drolsen/r2-periscope-lighting/assets/329545608_787965672744725_6274756382446998842_n.jpg

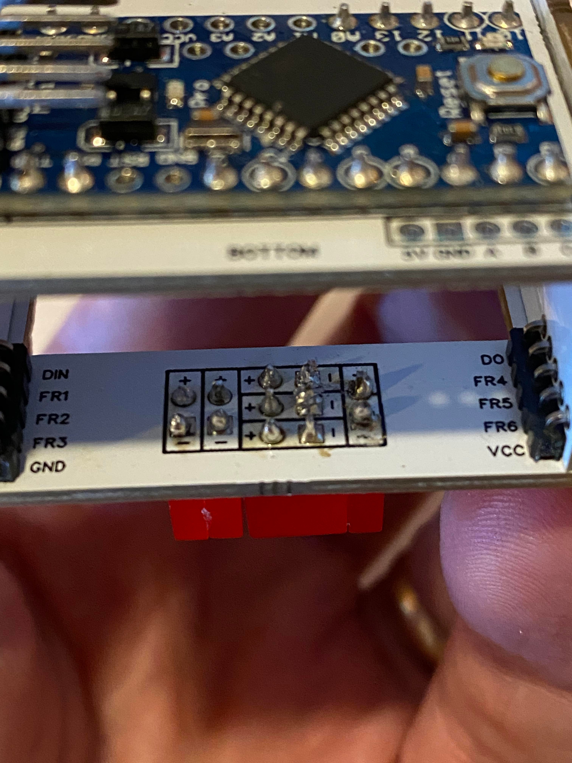
assets/329545608_787965672744725_6274756382446998842_n.jpg
