drolsen/r2-periscope-lighting/assets/329946529_3398057897189218_7023022062316048752_n.jpg

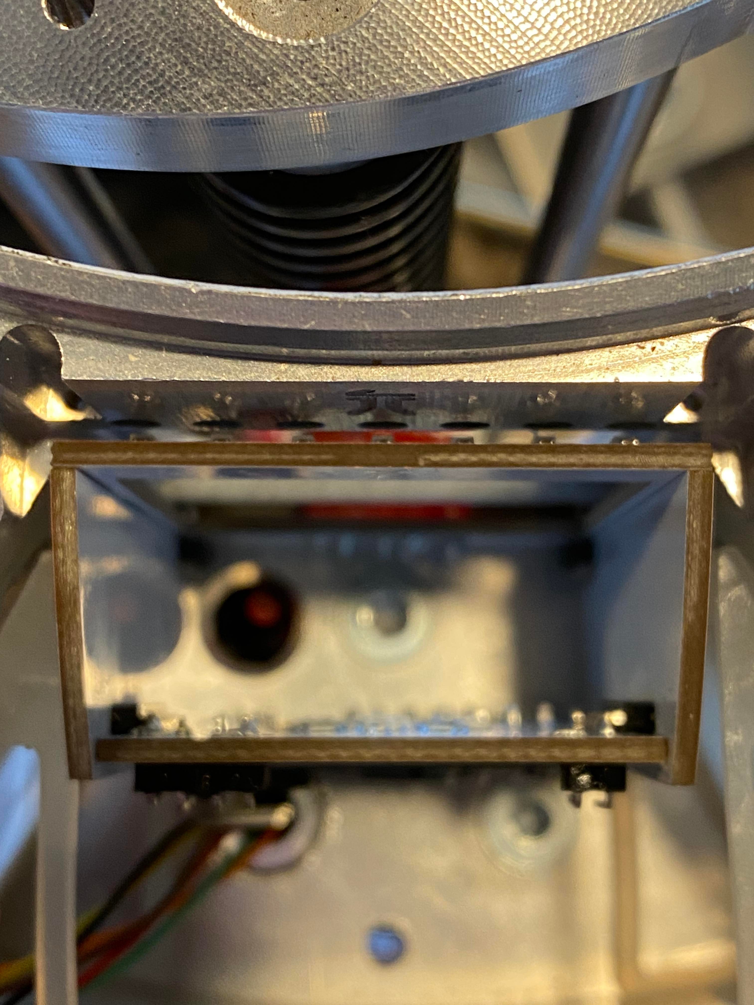
assets/329946529_3398057897189218_7023022062316048752_n.jpg
