drolsen/r2-periscope-lighting/assets/330140581_1176772722986566_4878100854022843440_n.jpg

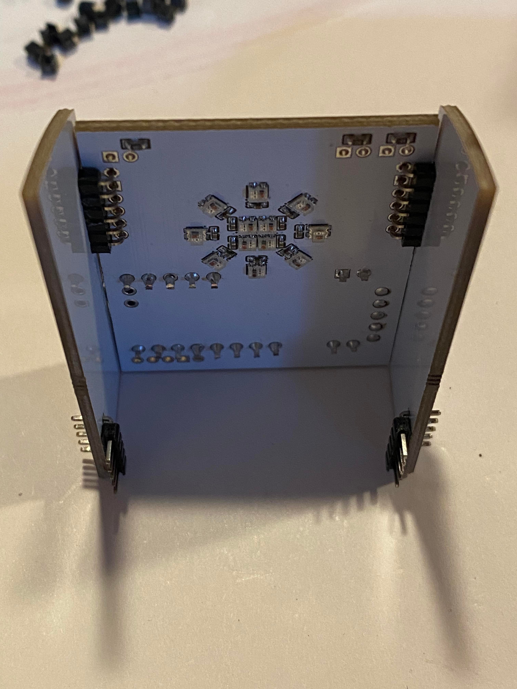
assets/330140581_1176772722986566_4878100854022843440_n.jpg
