drolsen/r2-periscope-lighting/assets/330237637_755844602558149_2887679224350733266_n.jpg

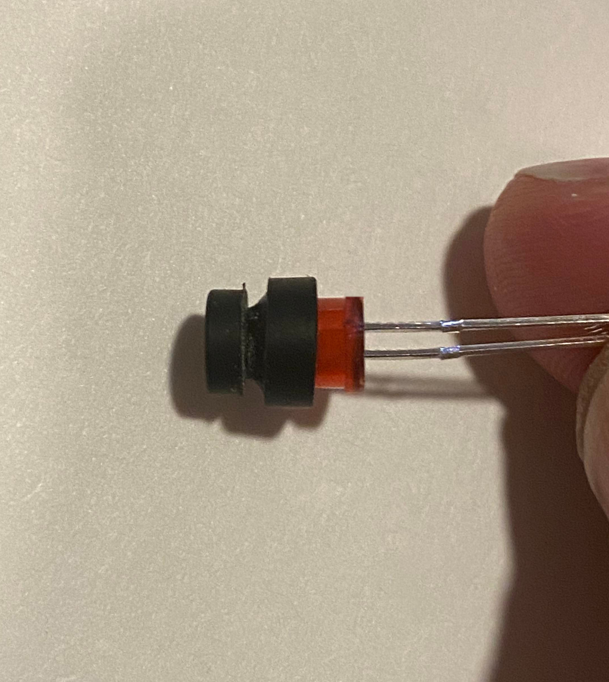
assets/330237637_755844602558149_2887679224350733266_n.jpg
