drolsen/r2-periscope-lighting/assets/336583348_1359087688268393_5020265776512630754_n.jpg

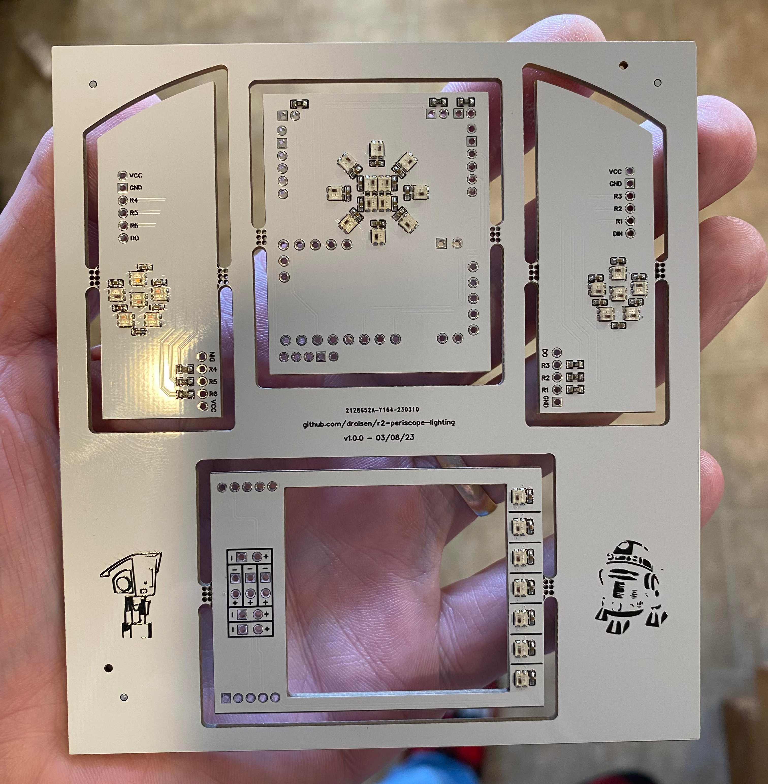
assets/336583348_1359087688268393_5020265776512630754_n.jpg
