drolsen/r2-periscope-lighting/assets/336612819_212626751346607_8498144002809746139_n.jpg

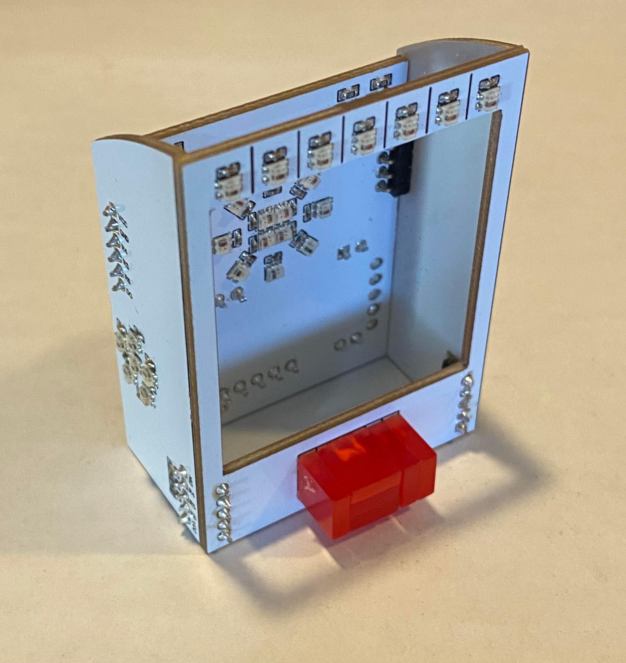
assets/336612819_212626751346607_8498144002809746139_n.jpg
