drolsen/r2-periscope-lighting/assets/336630692_2085747125148480_5399964535549881073_n.jpg

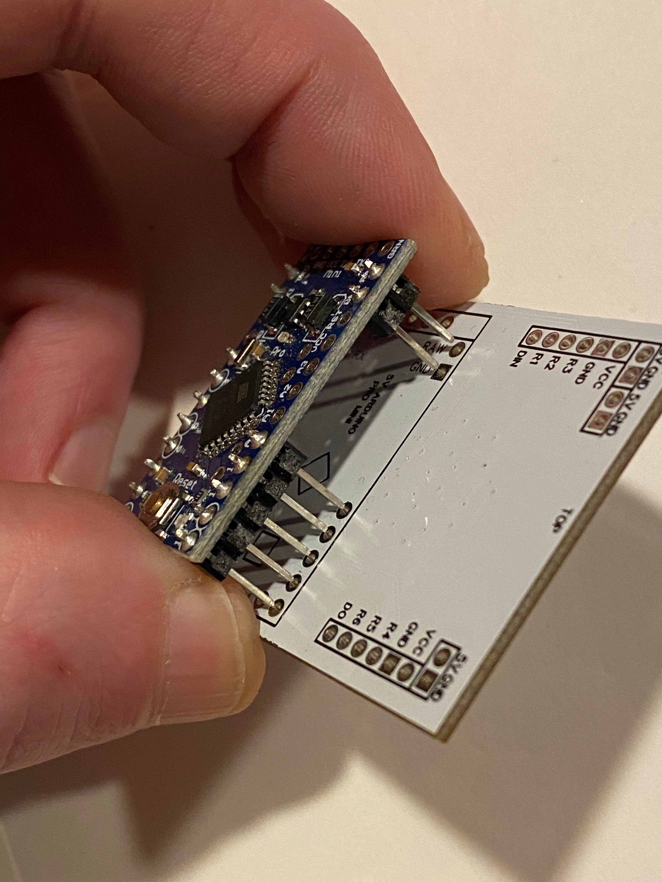
assets/336630692_2085747125148480_5399964535549881073_n.jpg
