drolsen/r2-periscope-lighting/assets/336634593_1632840413847791_8833610450574456791_n.jpg

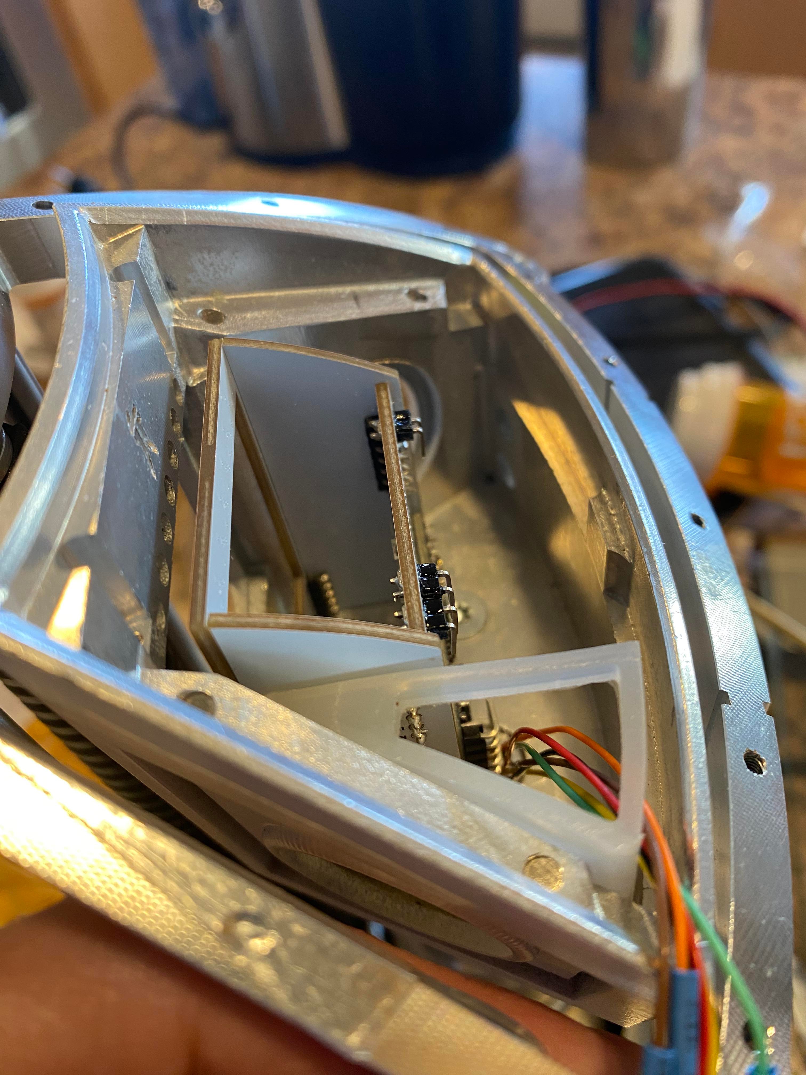
assets/336634593_1632840413847791_8833610450574456791_n.jpg
