drolsen/r2-periscope-lighting/assets/336643133_749938070041461_5090229318301993408_n.jpg

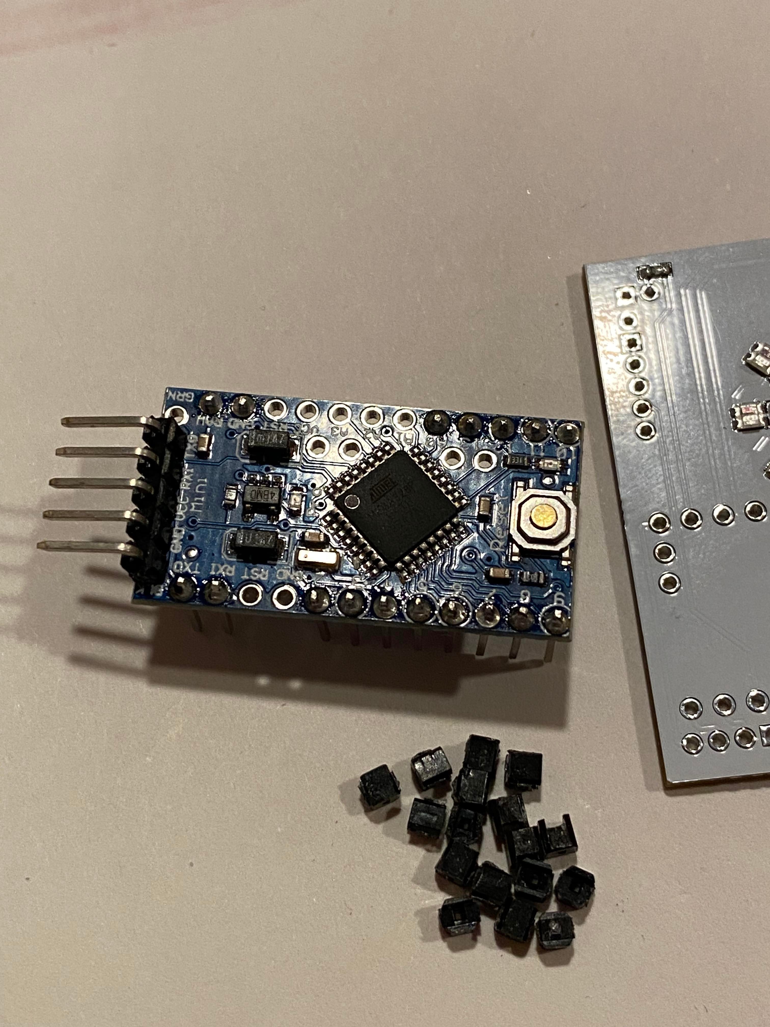
assets/336643133_749938070041461_5090229318301993408_n.jpg
