drolsen/r2-periscope-lighting/assets/336646238_229451316157610_1500926734936999446_n.jpg

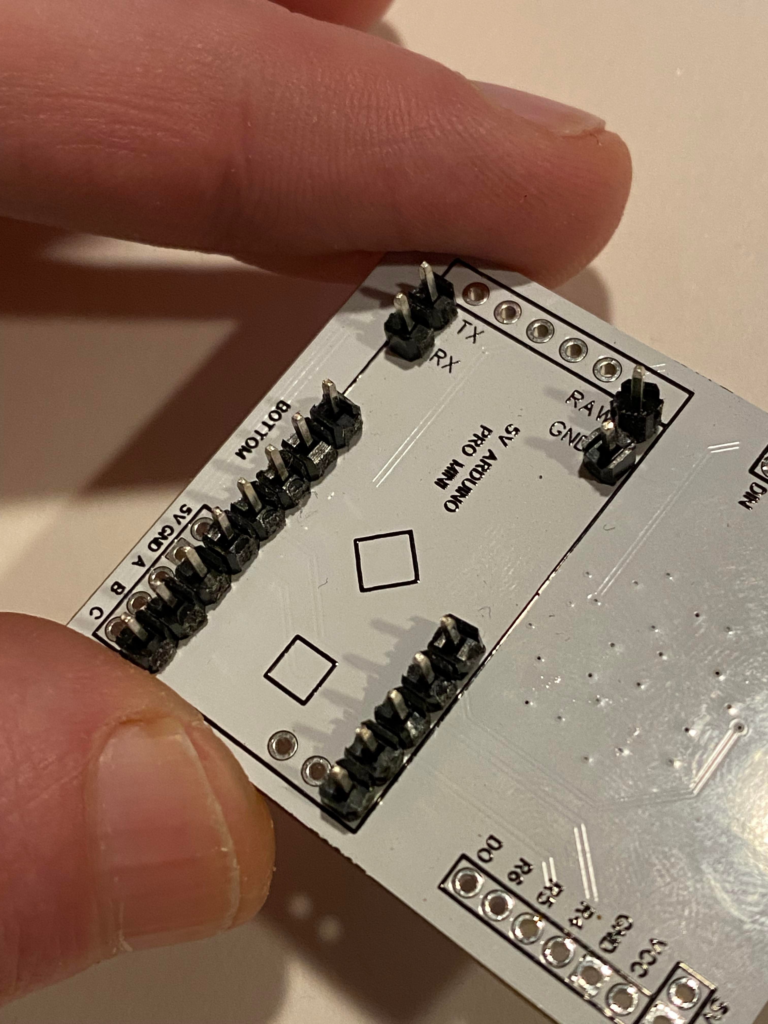
assets/336646238_229451316157610_1500926734936999446_n.jpg
