drolsen/r2-periscope-lighting/assets/336648805_155341664117025_93847598374509q8374_n.jpg

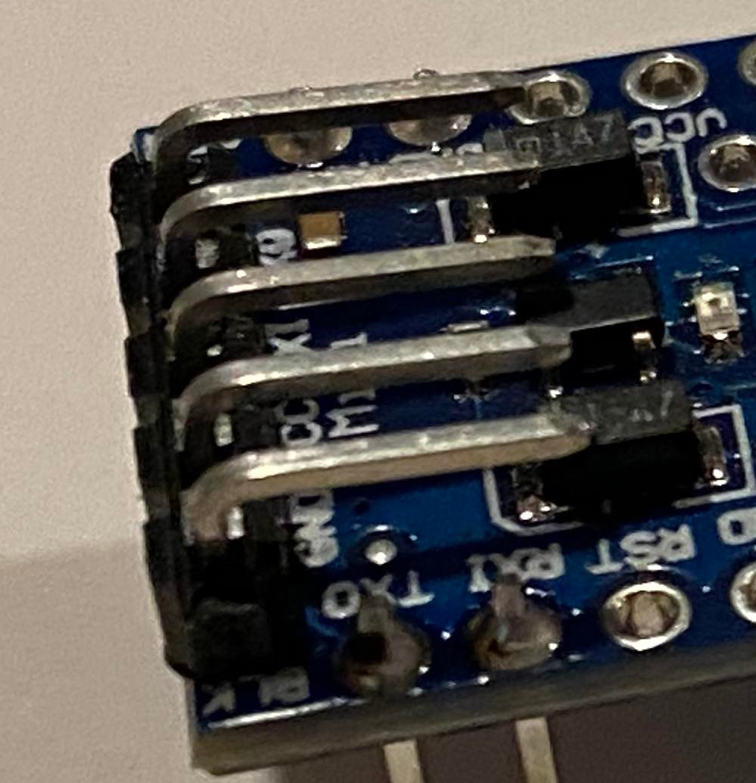
assets/336648805_155341664117025_93847598374509q8374_n.jpg
