drolsen/r2-periscope-lighting/assets/336648805_155341664117025_7592663786943222012_n.jpg

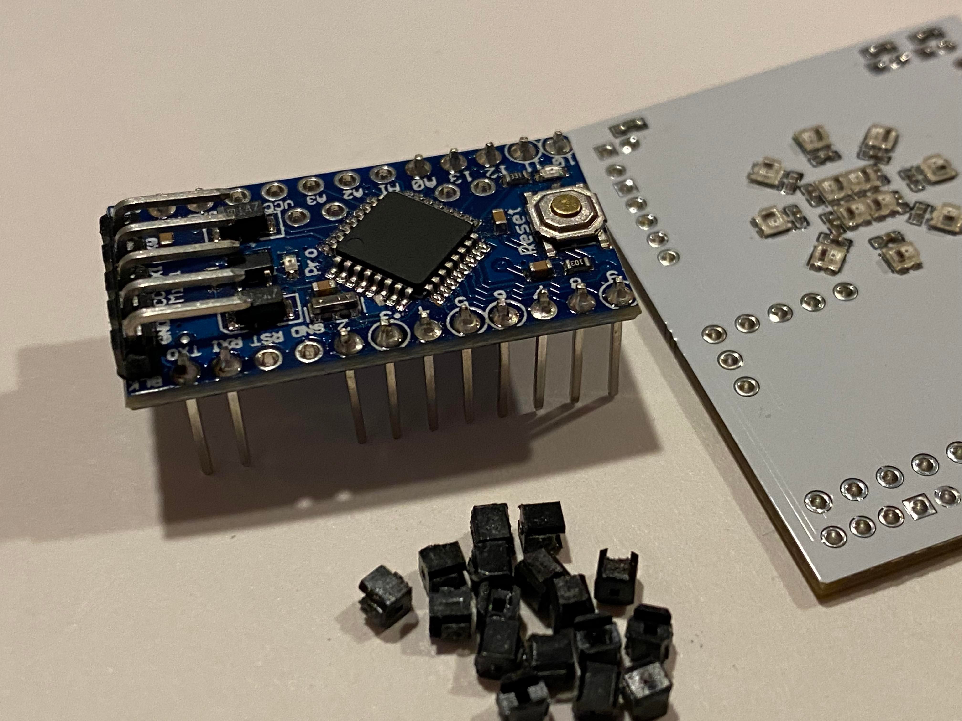
assets/336648805_155341664117025_7592663786943222012_n.jpg
