drolsen/r2-periscope-lighting/assets/336650088_955661678923347_95887453174213963_n.jpg

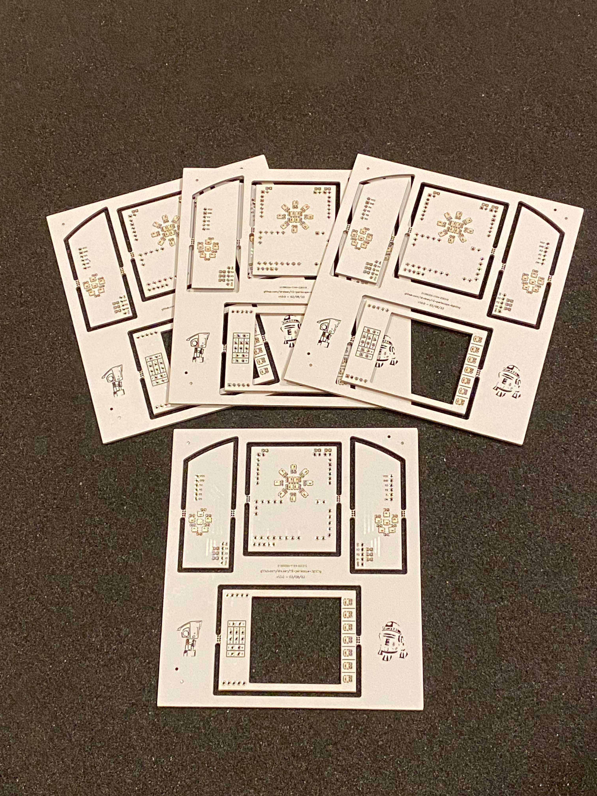
assets/336650088_955661678923347_95887453174213963_n.jpg
