drolsen/r2-periscope-lighting/assets/336652210_146992861645513_2133253247922061453_n.jpg

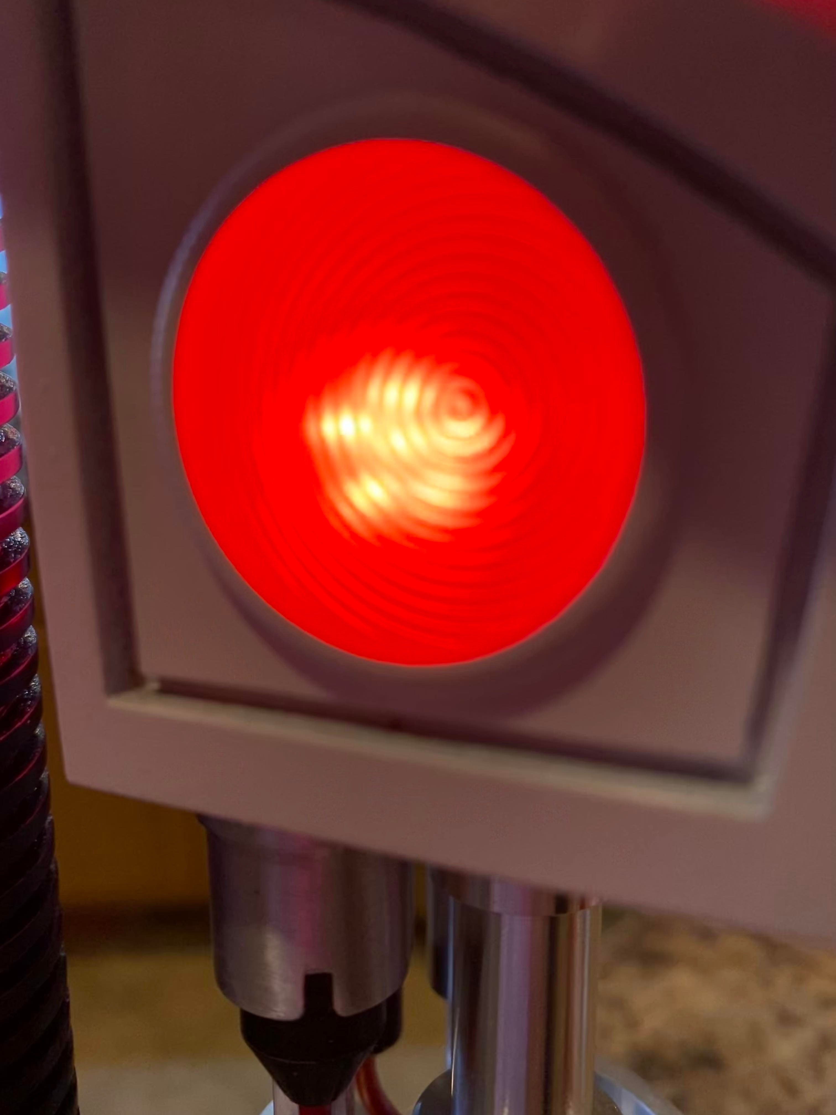
assets/336652210_146992861645513_2133253247922061453_n.jpg
