drolsen/r2-periscope-lighting/assets/336652988_1221817398455848_6877816285766562561_n.jpg

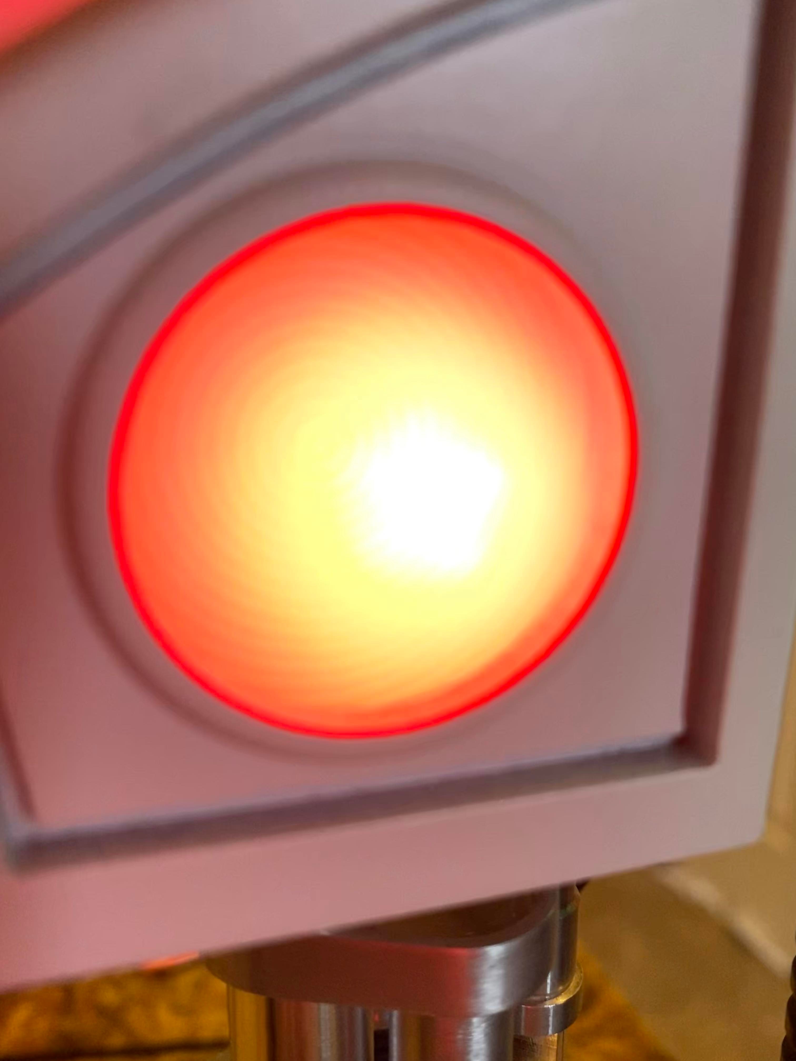
assets/336652988_1221817398455848_6877816285766562561_n.jpg
