drolsen/r2-periscope-lighting/assets/336654507_557893633128408_7048110893152010657_n.jpg

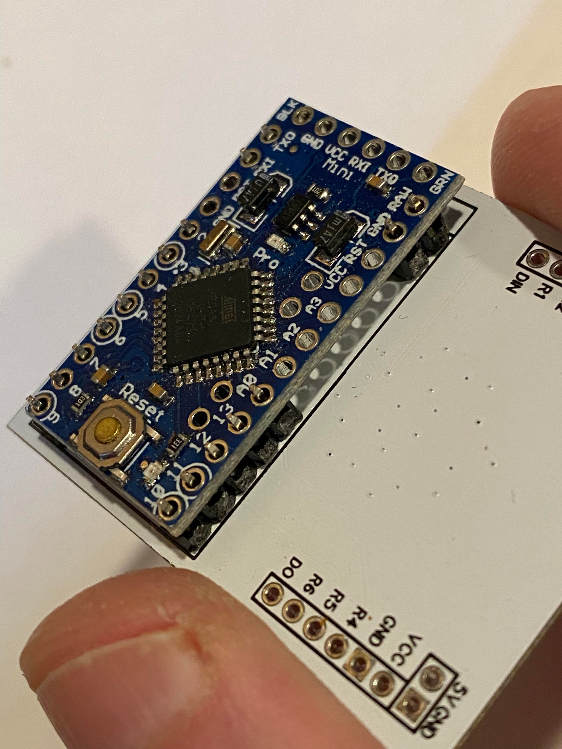
assets/336654507_557893633128408_7048110893152010657_n.jpg
