drolsen/r2-periscope-lighting/assets/336655963_2727371454069084_6634626331095543156_n.jpg

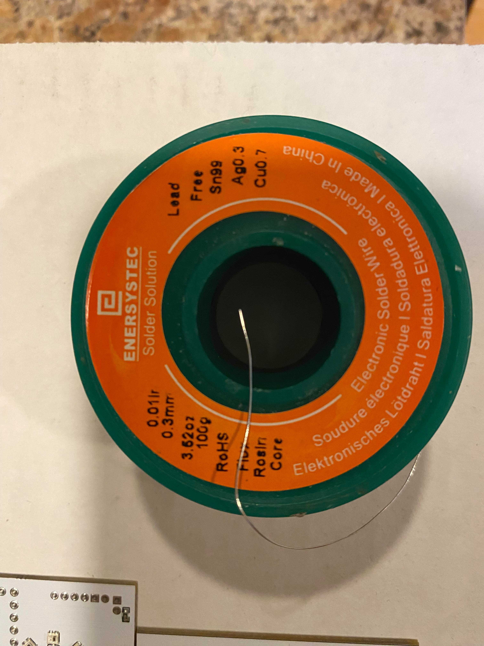
assets/336655963_2727371454069084_6634626331095543156_n.jpg
