drolsen/r2-periscope-lighting/assets/336656577_208245721811248_5027375010276381382_n.jpg

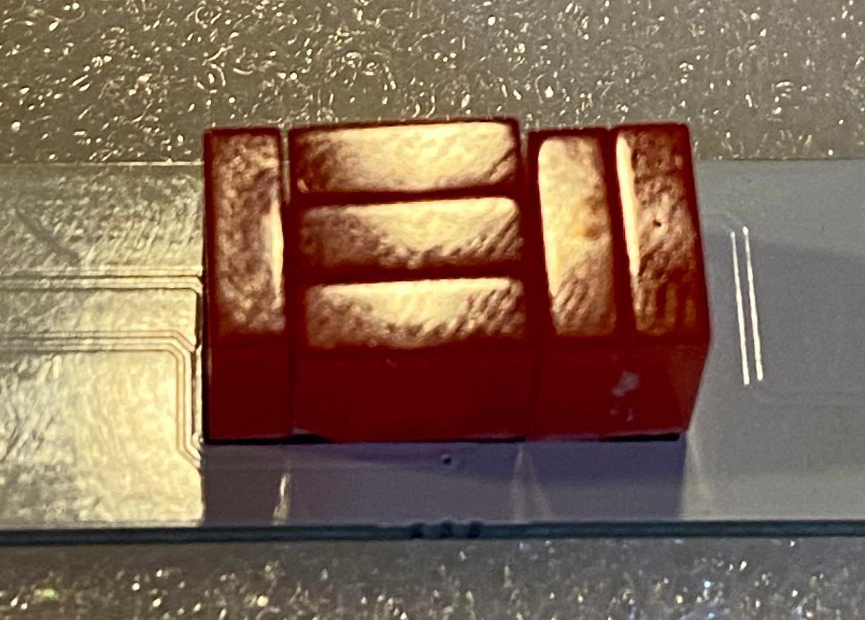
assets/336656577_208245721811248_5027375010276381382_n.jpg
