drolsen/r2-periscope-lighting/assets/336674563_130055486537326_960620624127797083_n.jpg

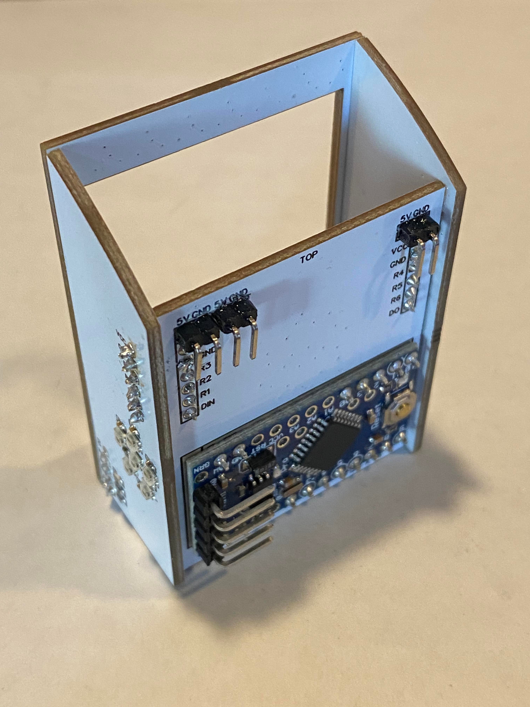
assets/336674563_130055486537326_960620624127797083_n.jpg
