drolsen/r2-periscope-lighting/assets/336676215_763743515095781_526933514709805942_n.jpg

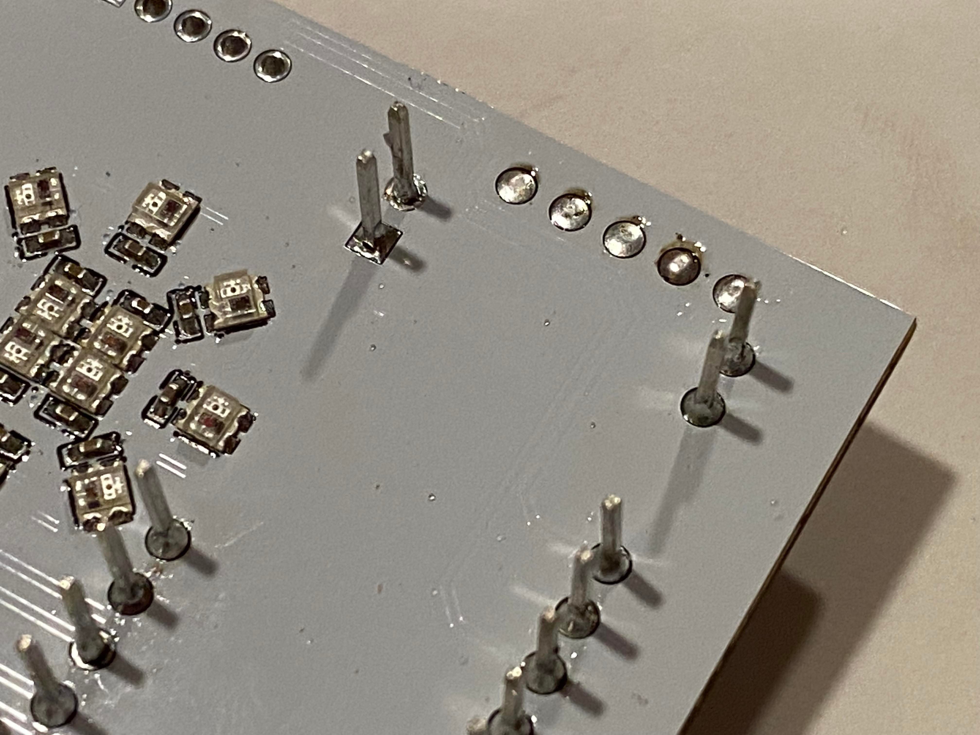
assets/336676215_763743515095781_526933514709805942_n.jpg
