drolsen/r2-periscope-lighting/assets/336676218_1423926755043374_4888183736791401821_n.jpg

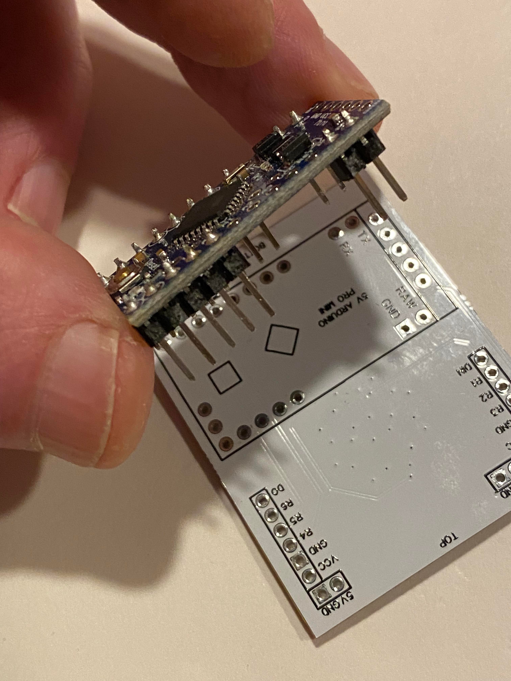
assets/336676218_1423926755043374_4888183736791401821_n.jpg
