drolsen/r2-periscope-lighting/assets/336762101_140780122016754_2259027312010947617_n.jpg

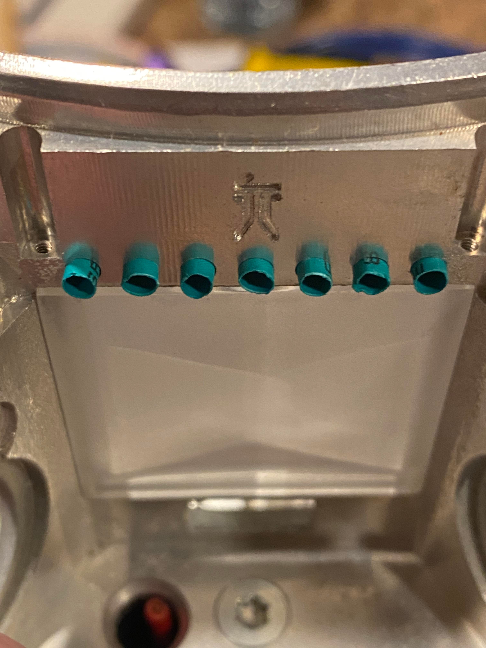
assets/336762101_140780122016754_2259027312010947617_n.jpg
