drolsen/r2-periscope-lighting/assets/336774285_554087970160996_1432412874619068593_n.jpg

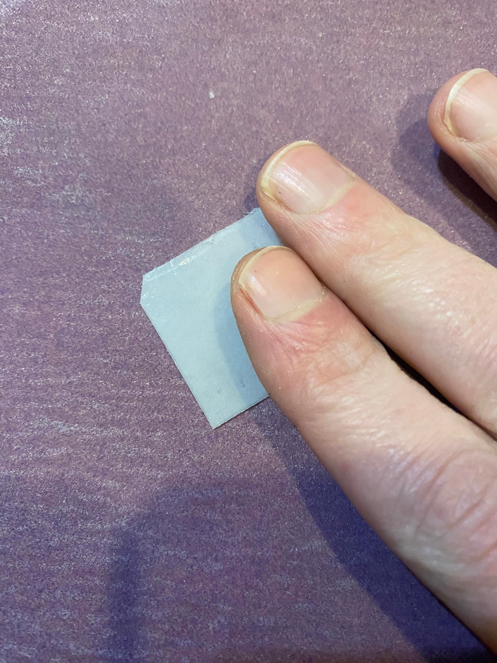
assets/336774285_554087970160996_1432412874619068593_n.jpg
