drolsen/r2-periscope-lighting/assets/336782065_769995744817289_480746282116714506_n.jpg

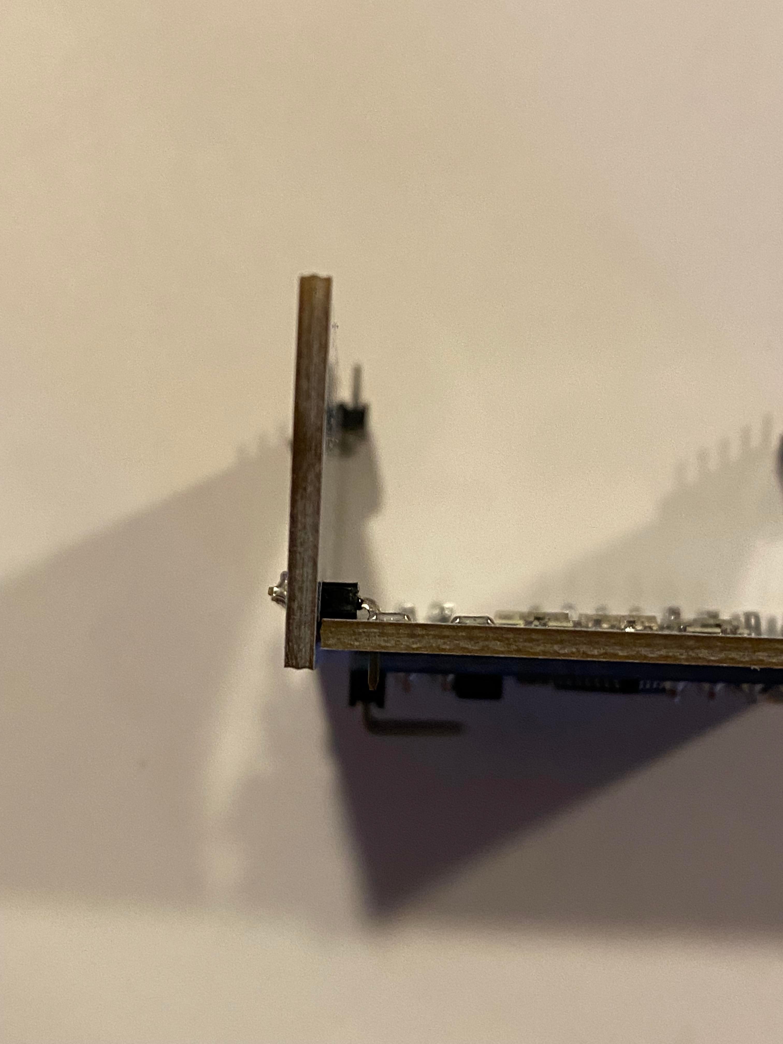
assets/336782065_769995744817289_480746282116714506_n.jpg
