drolsen/r2-periscope-lighting/assets/336802224_611826760356297_9049021178184410833_n.jpg

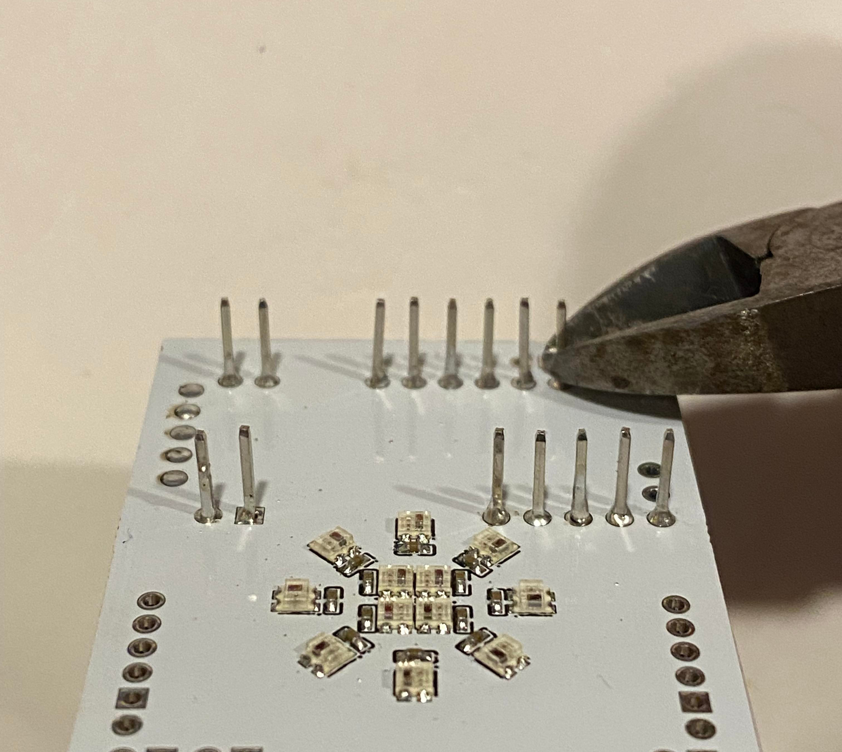
assets/336802224_611826760356297_9049021178184410833_n.jpg
