drolsen/r2-periscope-lighting/assets/336858418_887466352534189_1731890954181260684_n.jpg

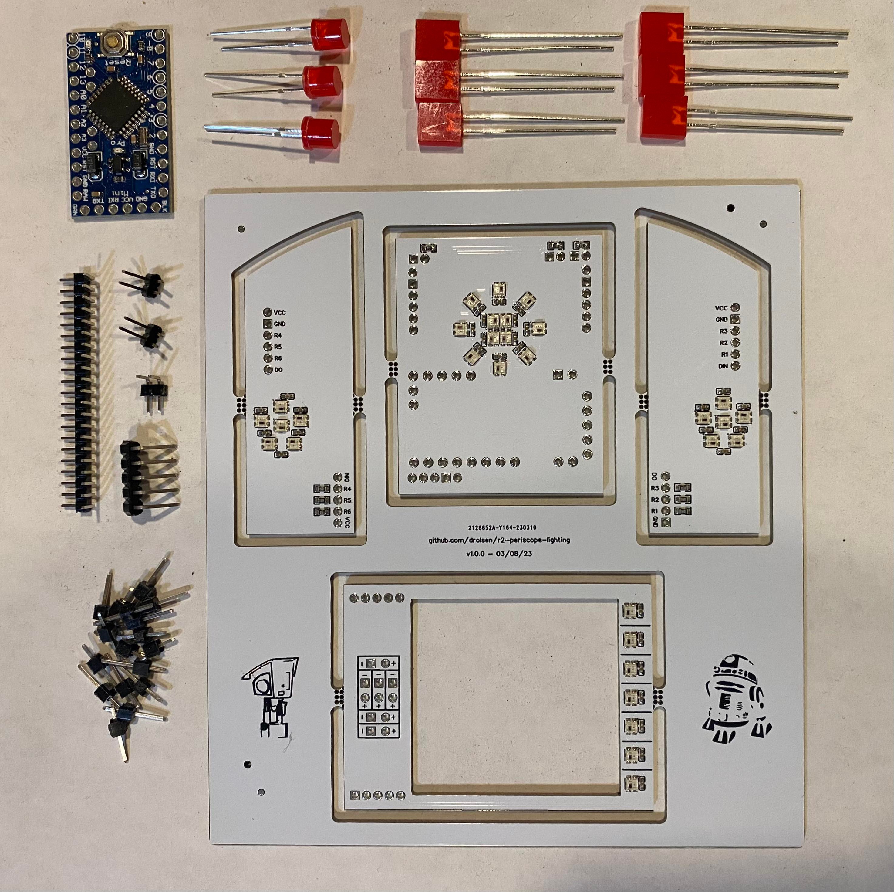
assets/336858418_887466352534189_1731890954181260684_n.jpg
