drolsen/r2-periscope-lighting/assets/336882048_944176487019811_1727440528449711896_n.jpg

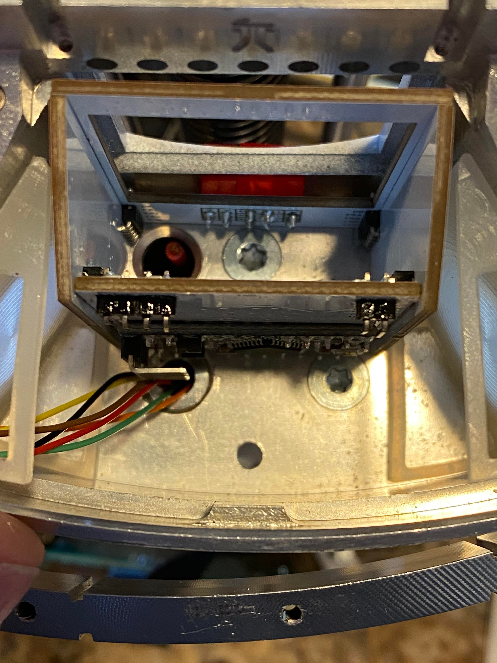
assets/336882048_944176487019811_1727440528449711896_n.jpg
