drolsen/r2-periscope-lighting/assets/336910001_962262608291722_509679109615035891_n.jpg

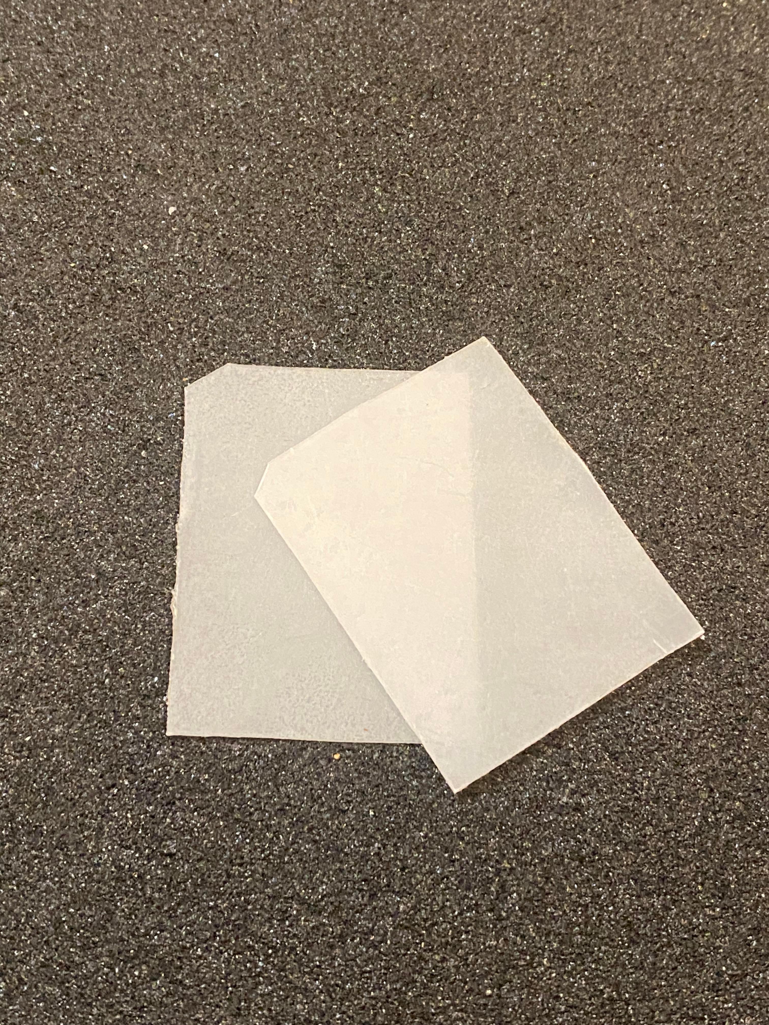
assets/336910001_962262608291722_509679109615035891_n.jpg
