drolsen/r2-periscope-lighting/assets/336953458_753239979686228_8079525611871128589_n.jpg

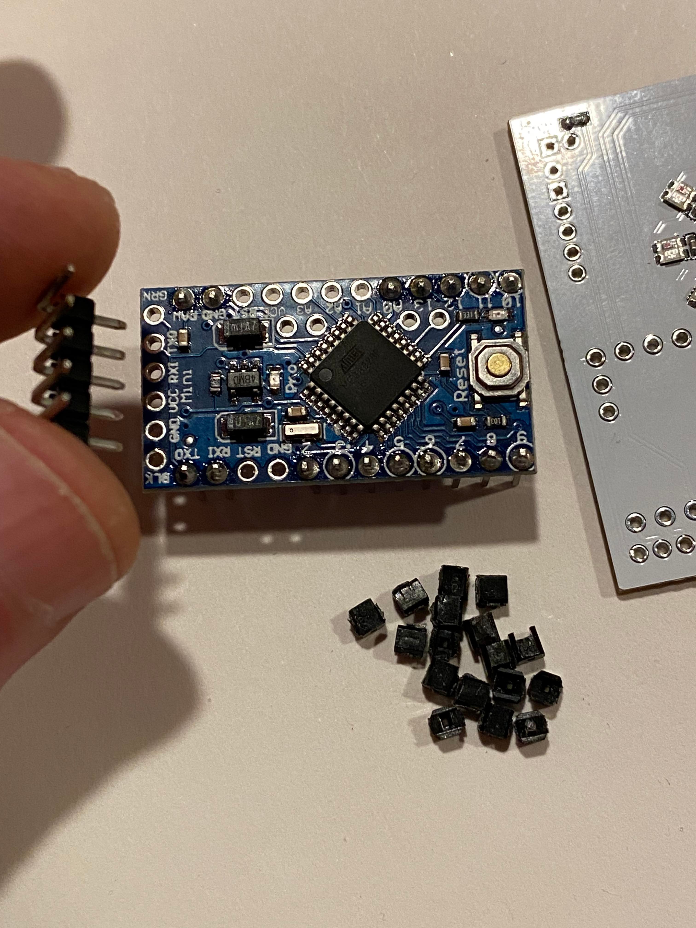
assets/336953458_753239979686228_8079525611871128589_n.jpg
