drolsen/r2-periscope-lighting/assets/336954538_926445541840880_992458918952481467_n.jpg

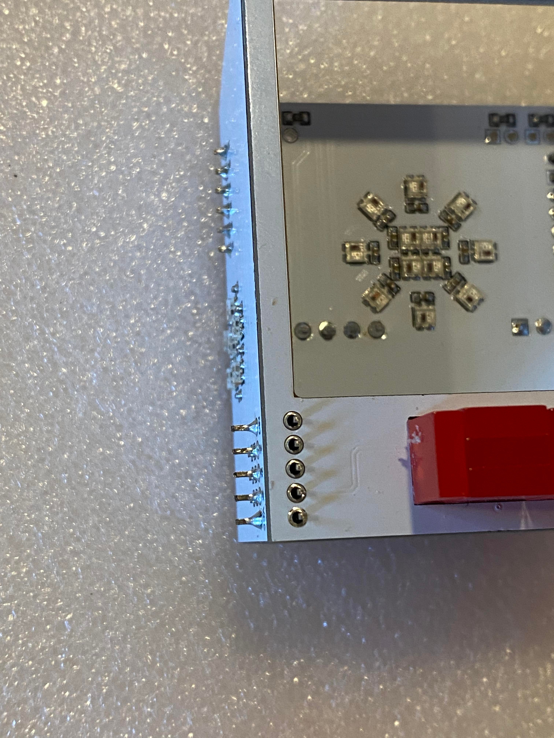
assets/336954538_926445541840880_992458918952481467_n.jpg
