drolsen/r2-periscope-lighting/assets/336974737_1384300059000098_4011215609476208007_n.jpg

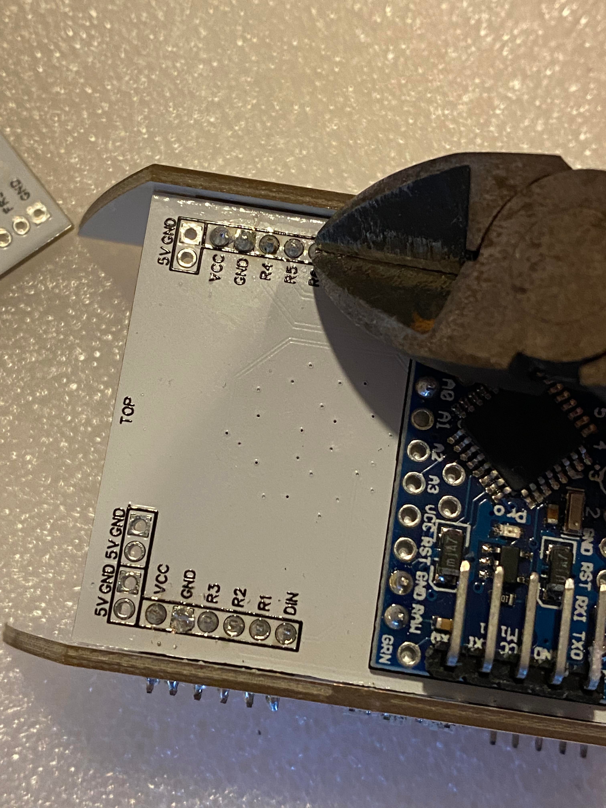
assets/336974737_1384300059000098_4011215609476208007_n.jpg
