drolsen/r2-periscope-lighting/assets/336978709_178584938370956_5981600598084434066_n.jpg

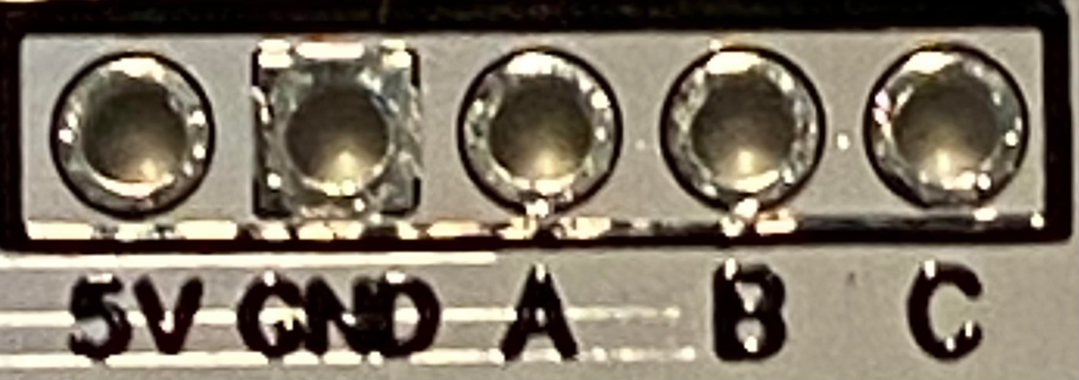
assets/336978709_178584938370956_5981600598084434066_n.jpg
