drolsen/r2-periscope-lighting/assets/336988302_238451835223995_1839003701058926174_n.jpg

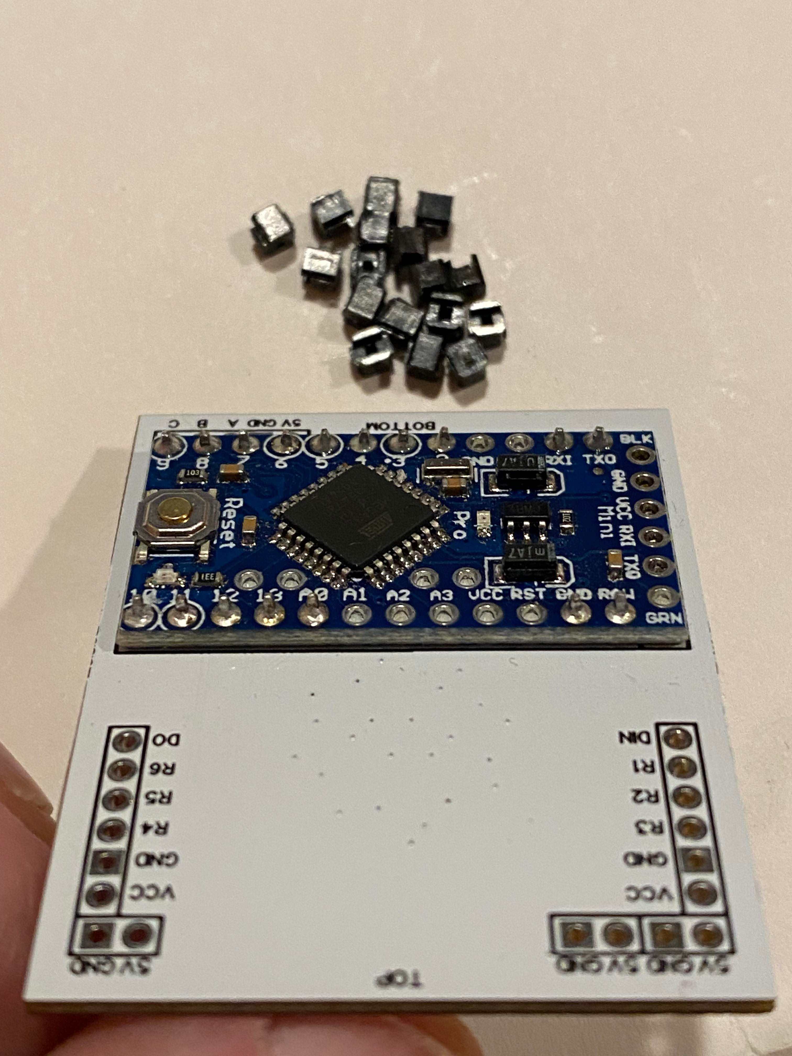
assets/336988302_238451835223995_1839003701058926174_n.jpg
