drolsen/r2-periscope-lighting/assets/337053296_767745125006024_4273821033584691869_n.jpg

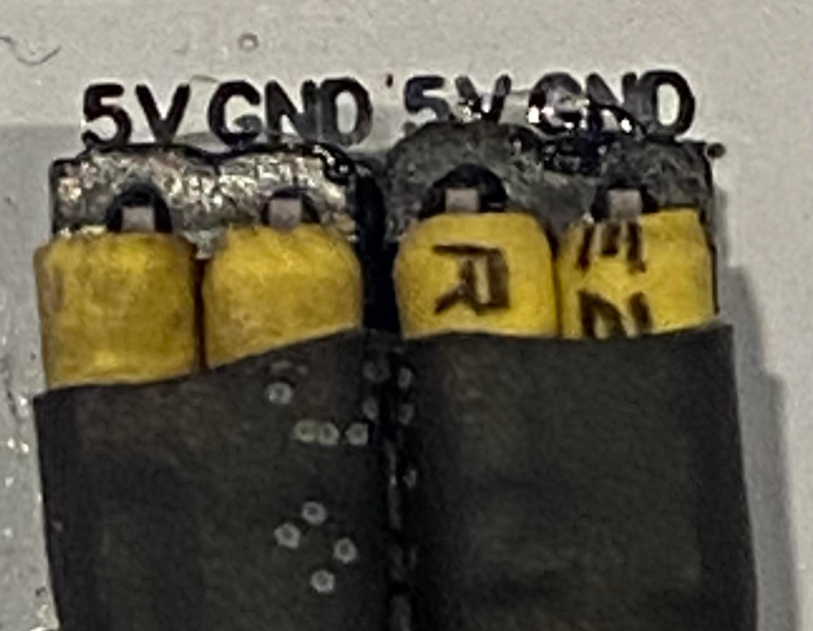
assets/337053296_767745125006024_4273821033584691869_n.jpg
