drolsen/r2-periscope-lighting/assets/337059061_1343841169793391_681237589327290217_n.jpg

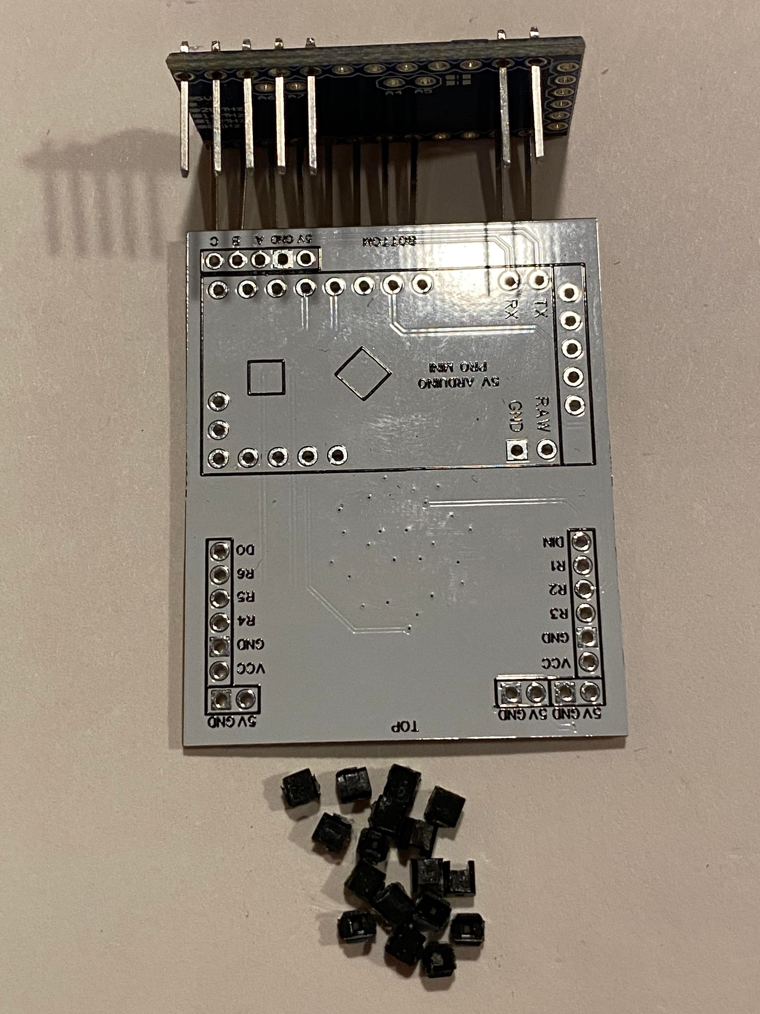
assets/337059061_1343841169793391_681237589327290217_n.jpg
