drolsen/r2-periscope-lighting/assets/337076968_3467573620138446_7653698219763336375_n.jpg

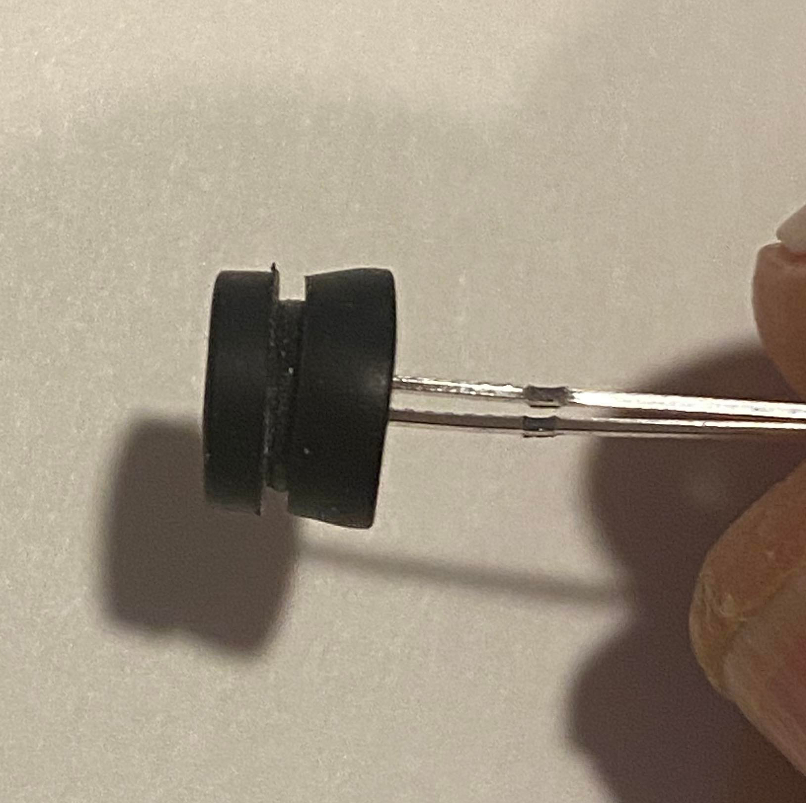
assets/337076968_3467573620138446_7653698219763336375_n.jpg
