drolsen/r2-periscope-lighting/assets/337102311_602154998597523_8643629842244105431_n.jpg

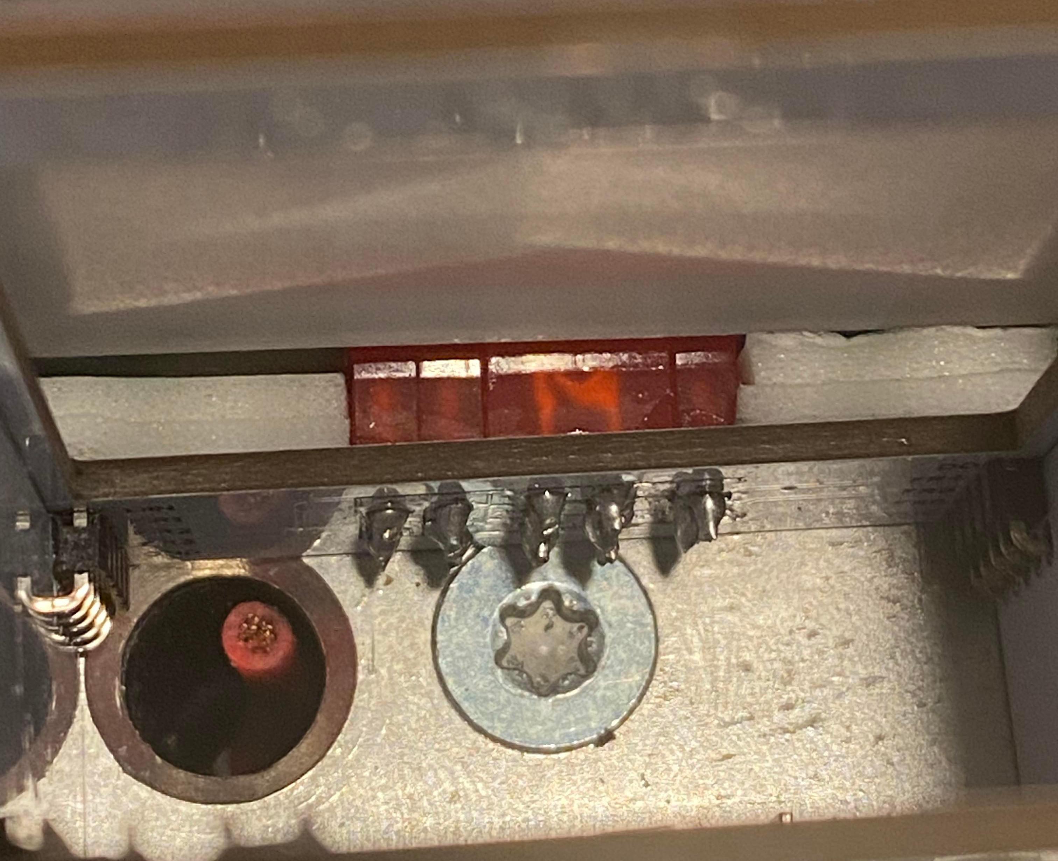
assets/337102311_602154998597523_8643629842244105431_n.jpg
