drolsen/r2-periscope-lighting/assets/337125022_598823498791530_1503493334196940726_n.jpg

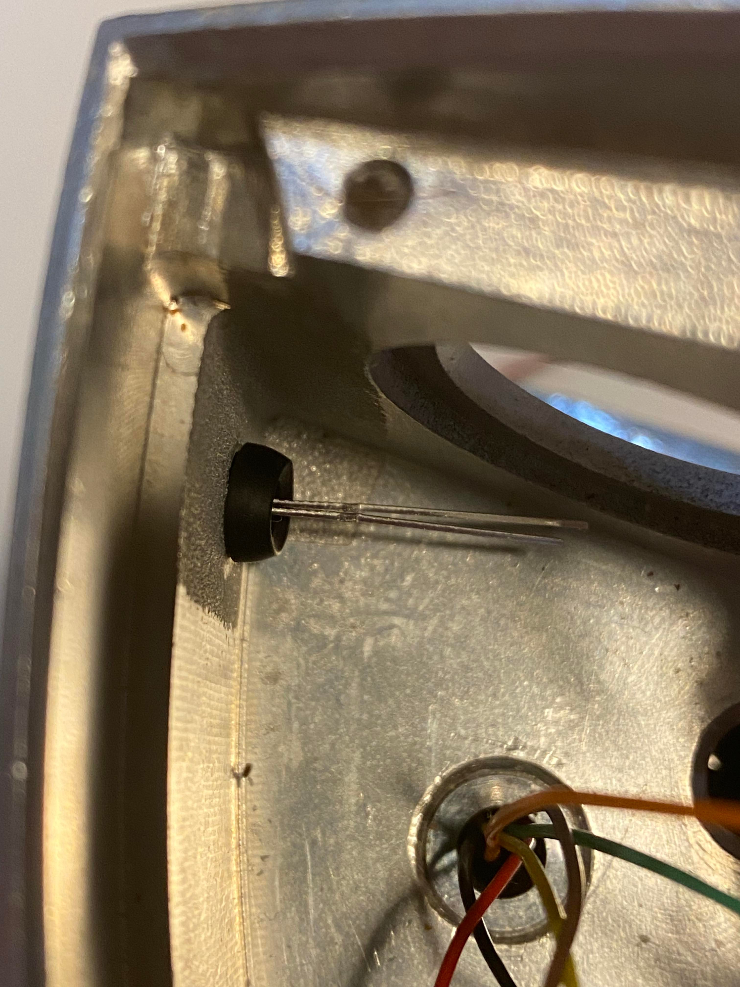
assets/337125022_598823498791530_1503493334196940726_n.jpg
