drolsen/r2-periscope-lighting/assets/337131278_3404263986559335_6530123598595243677_n.jpg

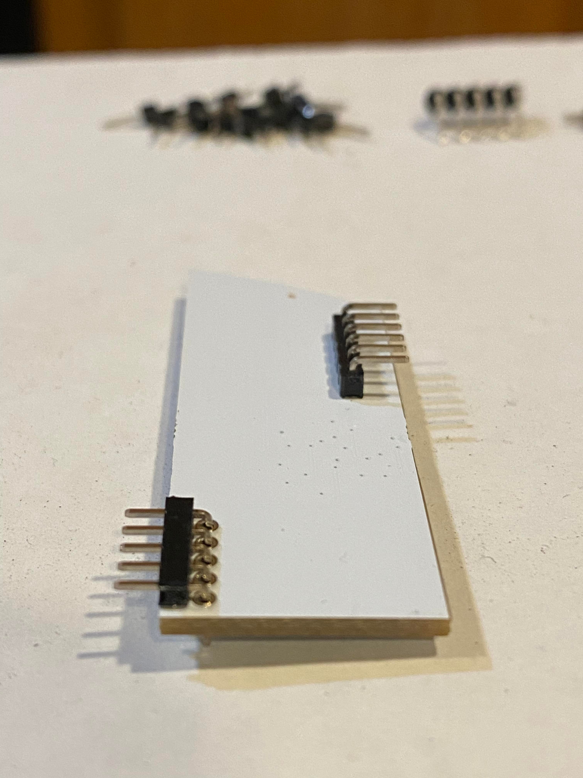
assets/337131278_3404263986559335_6530123598595243677_n.jpg
