drolsen/r2-periscope-lighting/assets/337312702_767708518035120_4002510822152139871_n.jpg

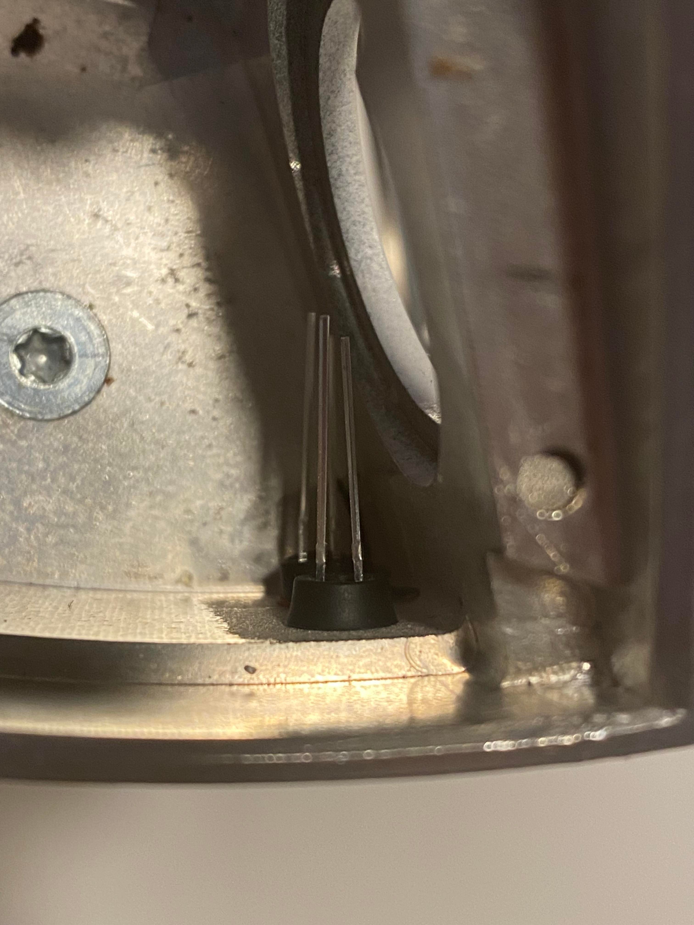
assets/337312702_767708518035120_4002510822152139871_n.jpg
