drolsen/r2-periscope-lighting/assets/337326929_697354182076062_739278119979212391_n.jpg

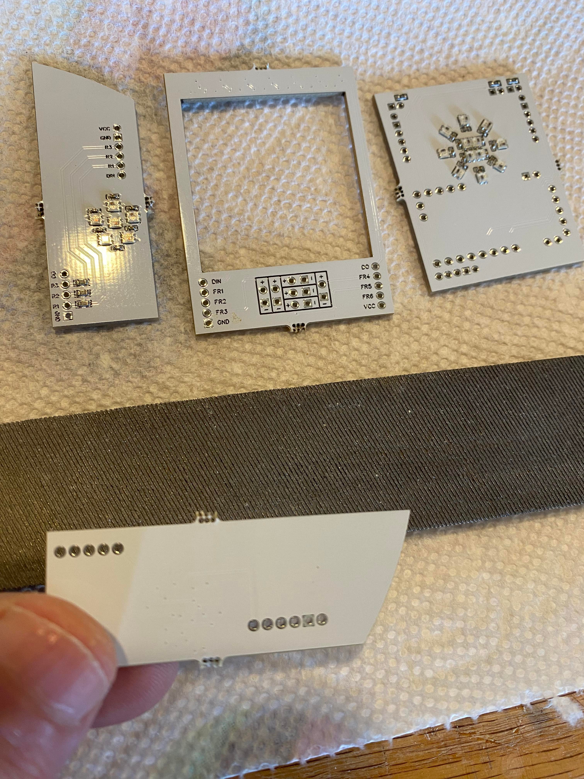
assets/337326929_697354182076062_739278119979212391_n.jpg
