drolsen/r2-periscope-lighting/assets/337430665_1330191880890299_2164580880244630802_n.jpg

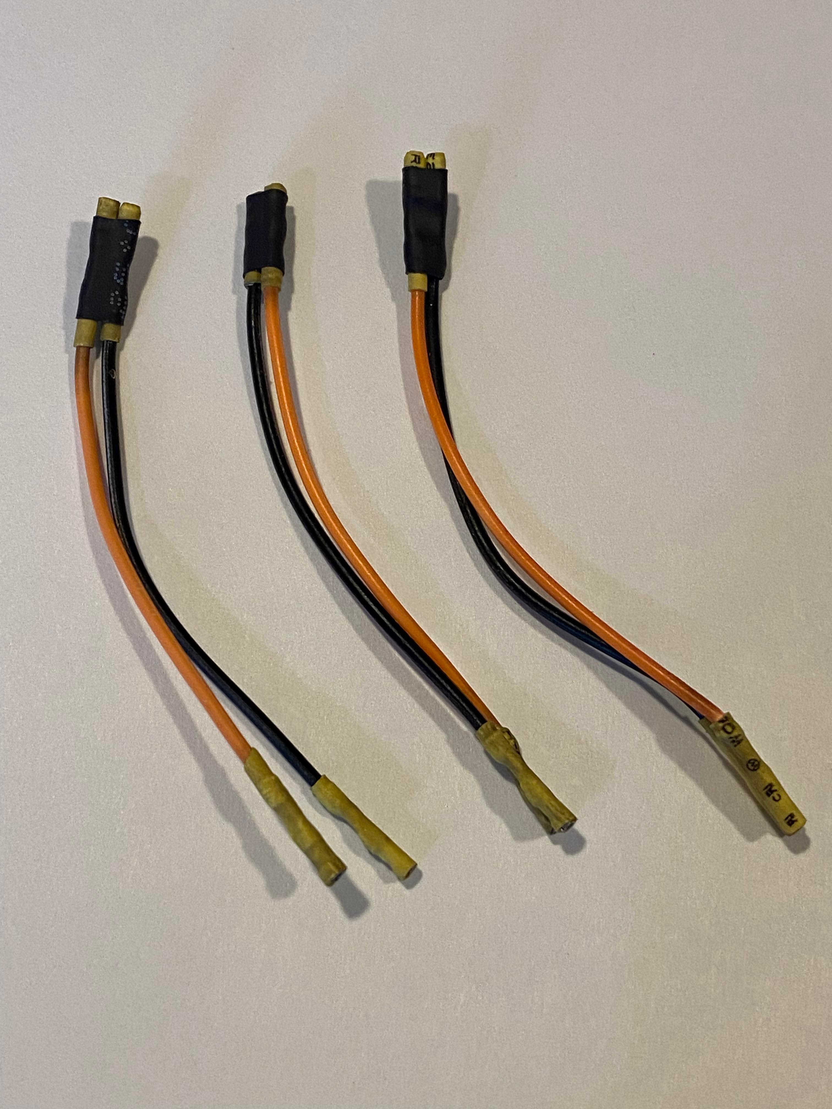
assets/337430665_1330191880890299_2164580880244630802_n.jpg
