drolsen/r2-periscope-lighting/assets/337437426_1242780033338704_8607743882371158958_n.jpg

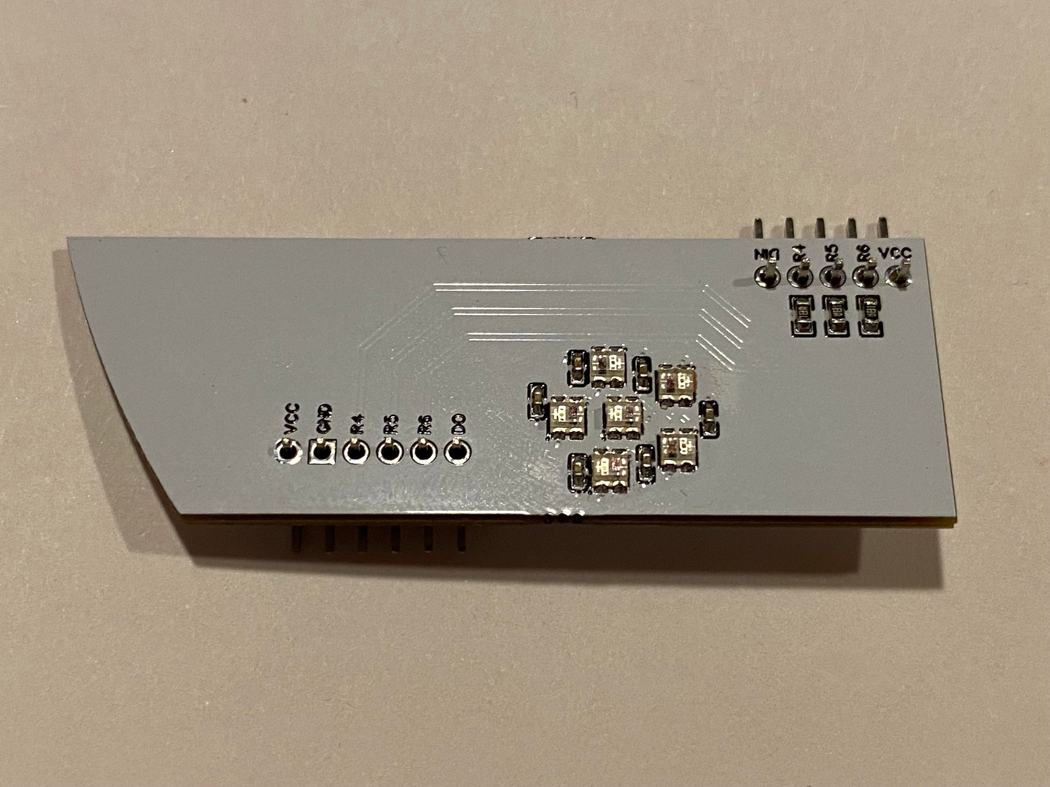
assets/337437426_1242780033338704_8607743882371158958_n.jpg
