drolsen/r2-periscope-lighting/assets/337509834_1648580835579013_2345284703102061359_n.jpg

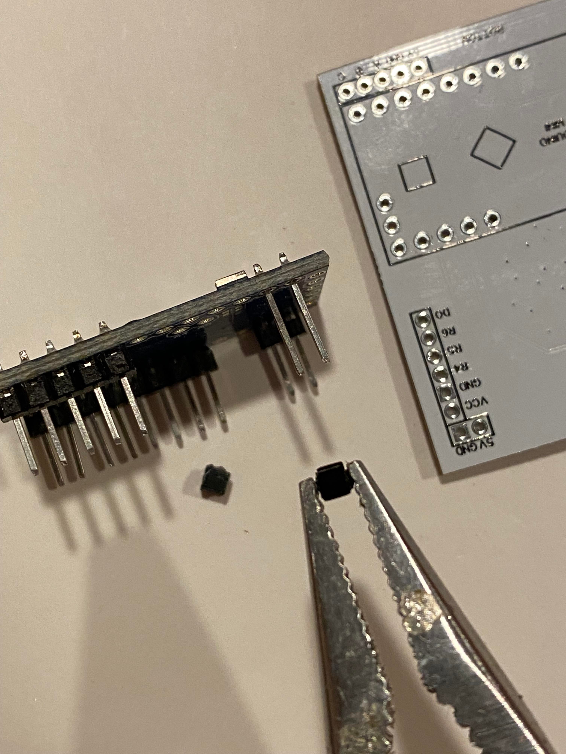
assets/337509834_1648580835579013_2345284703102061359_n.jpg
