drolsen/r2-periscope-lighting/assets/337527989_3113629652270110_7860070083218704774_n.jpg

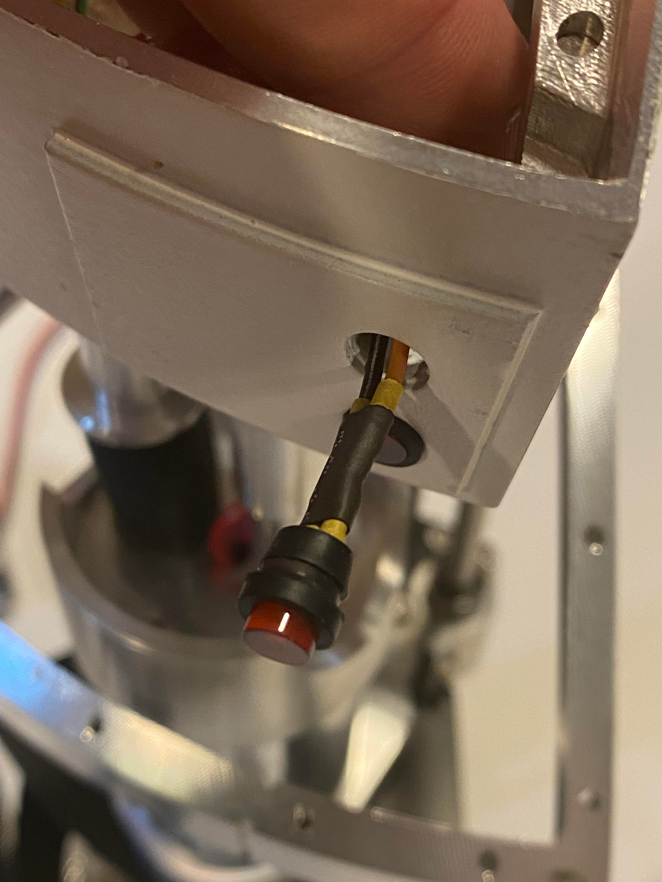
assets/337527989_3113629652270110_7860070083218704774_n.jpg
