drolsen/r2-periscope-lighting/assets/337577293_957165888985803_4228707793538416339_n.jpg

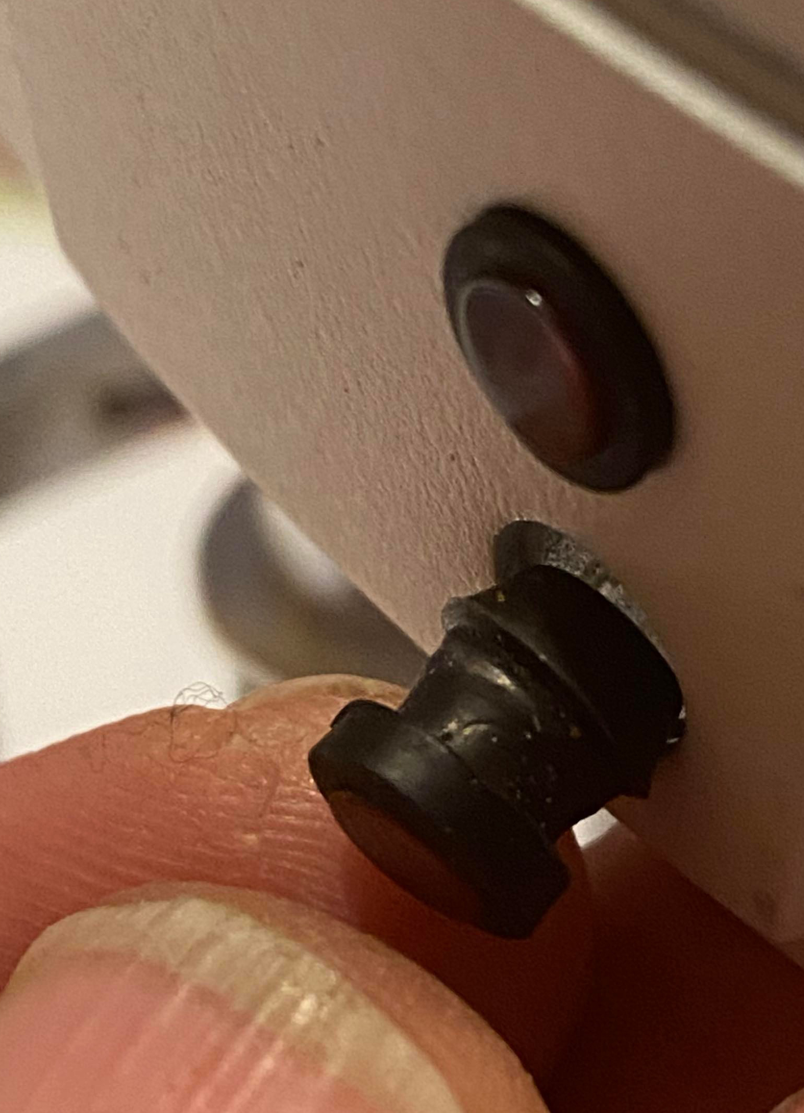
assets/337577293_957165888985803_4228707793538416339_n.jpg
