drolsen/r2-periscope-lighting/assets/337604403_576218807803695_5891221295153732761_n.jpg

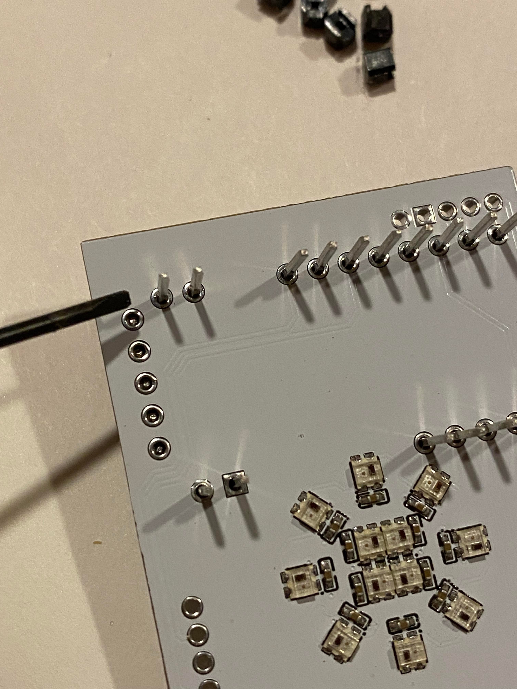
assets/337604403_576218807803695_5891221295153732761_n.jpg
