drolsen/r2-periscope-lighting/assets/337606039_520542230283870_7820957651189155970_n.jpg

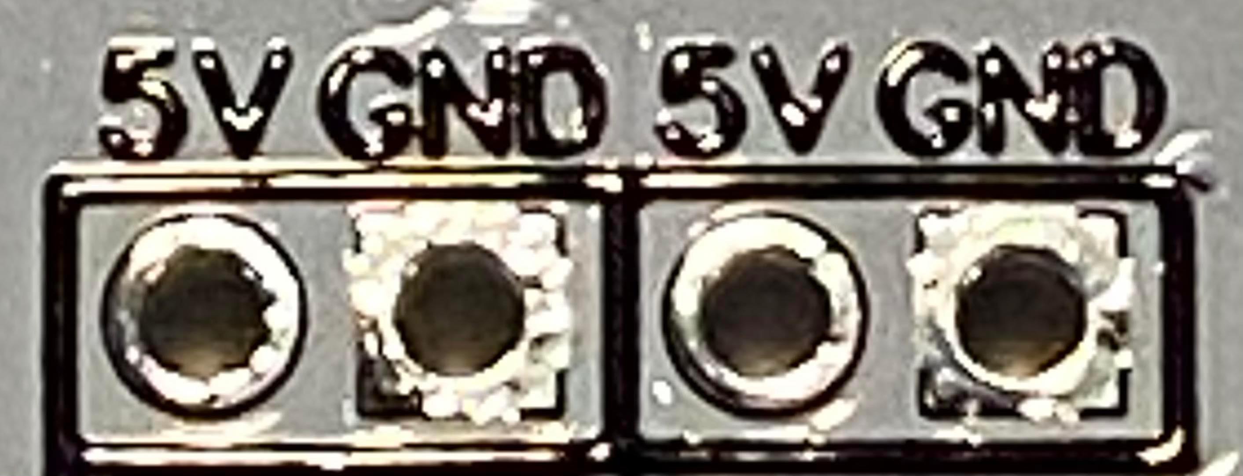
assets/337606039_520542230283870_7820957651189155970_n.jpg
