drolsen/r2-periscope-lighting/assets/337607260_1281717002421008_2037735765306753811_n.jpg

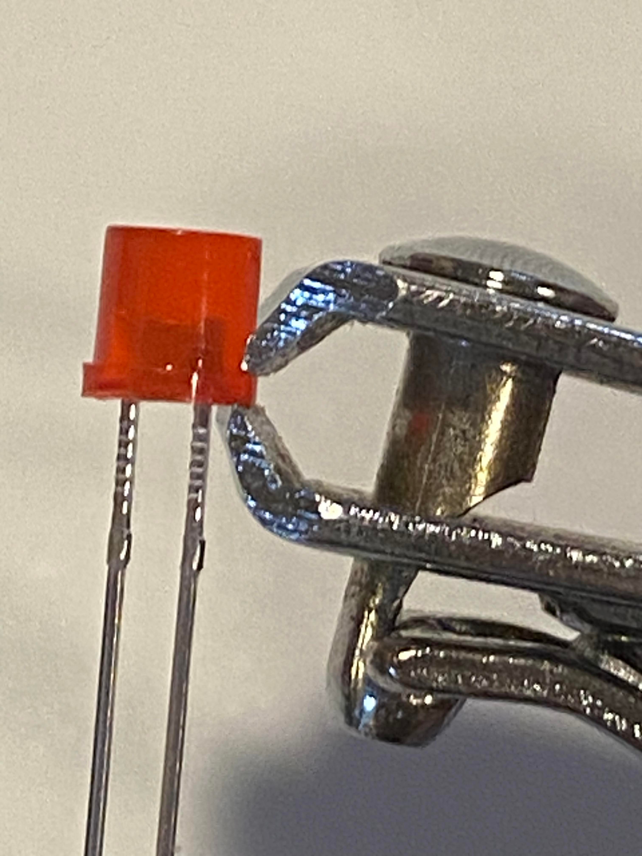
assets/337607260_1281717002421008_2037735765306753811_n.jpg
