drolsen/r2-periscope-lighting/assets/337635398_736080121514694_4125993924179733837_n.jpg

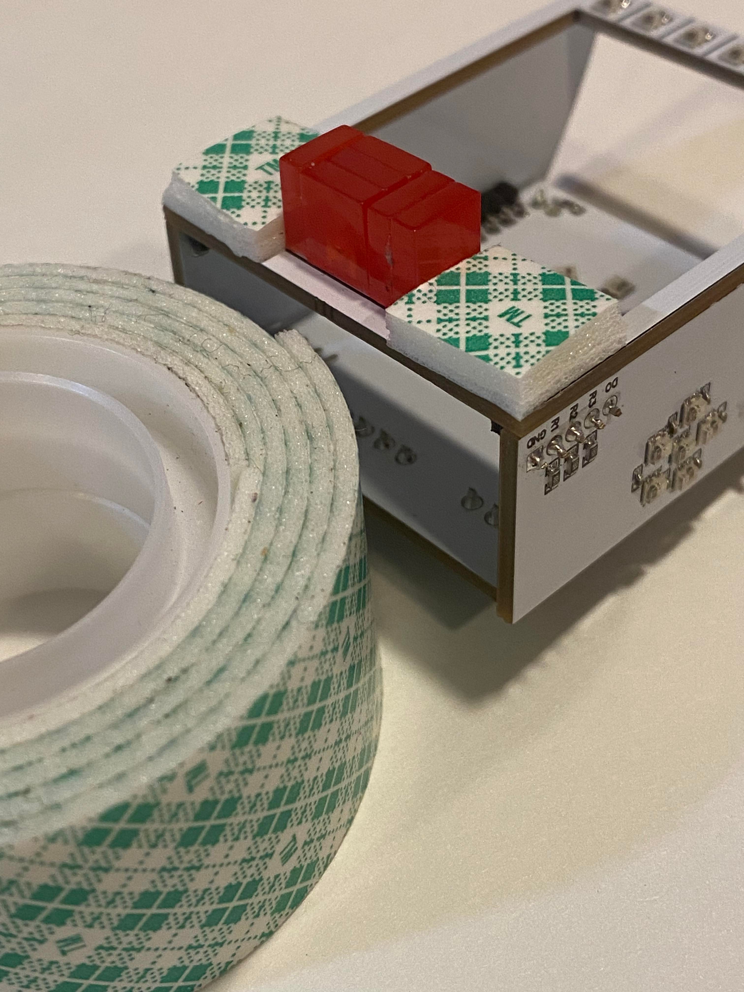
assets/337635398_736080121514694_4125993924179733837_n.jpg
