drolsen/r2-periscope-lighting/assets/337684261_688680399613634_2446779014030799641_n.jpg

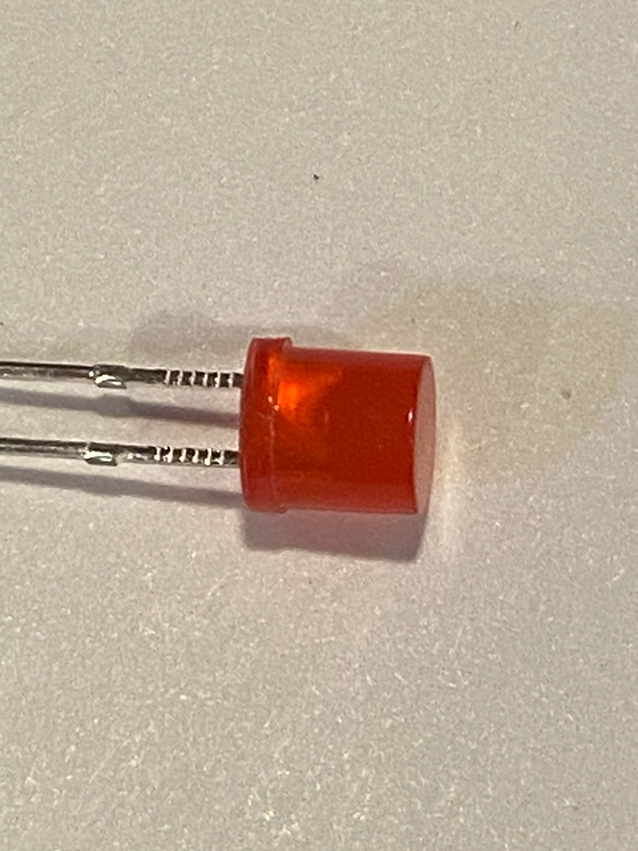
assets/337684261_688680399613634_2446779014030799641_n.jpg
