drolsen/r2-periscope-lighting/assets/337927002_164633022777300_1413733384161125463_n.jpg

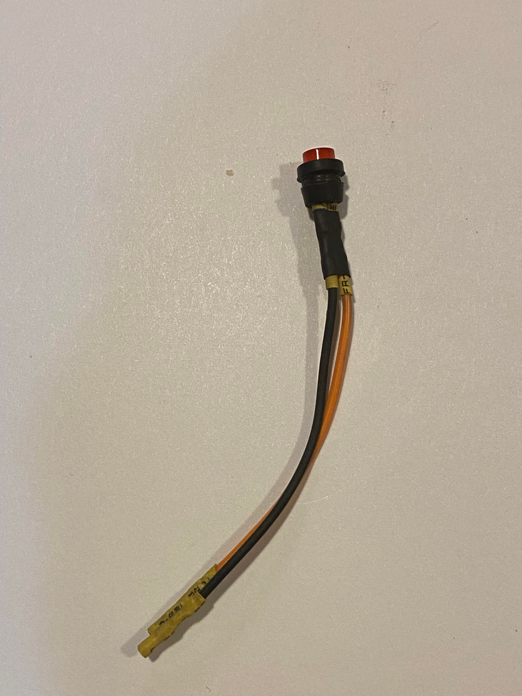
assets/337927002_164633022777300_1413733384161125463_n.jpg
