drolsen/r2-periscope-lighting/assets/338565213_963474577975506_4495961062662704930_n.jpg

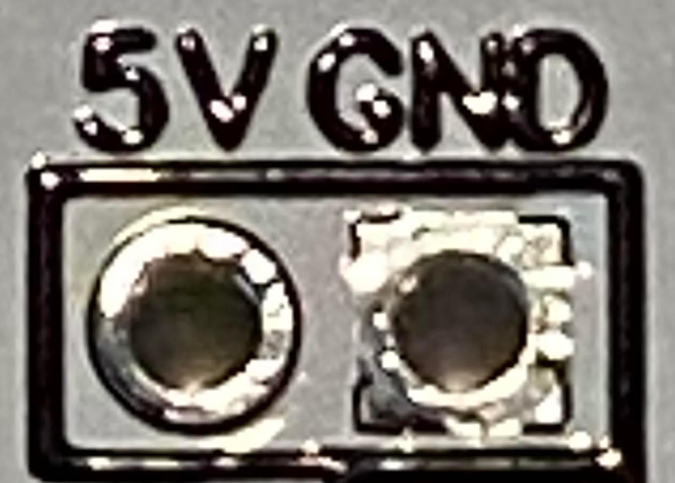
assets/338565213_963474577975506_4495961062662704930_n.jpg
