drolsen/r2-periscope-lighting/assets/338622038_1027298345303575_6589060000439139115_n.jpg

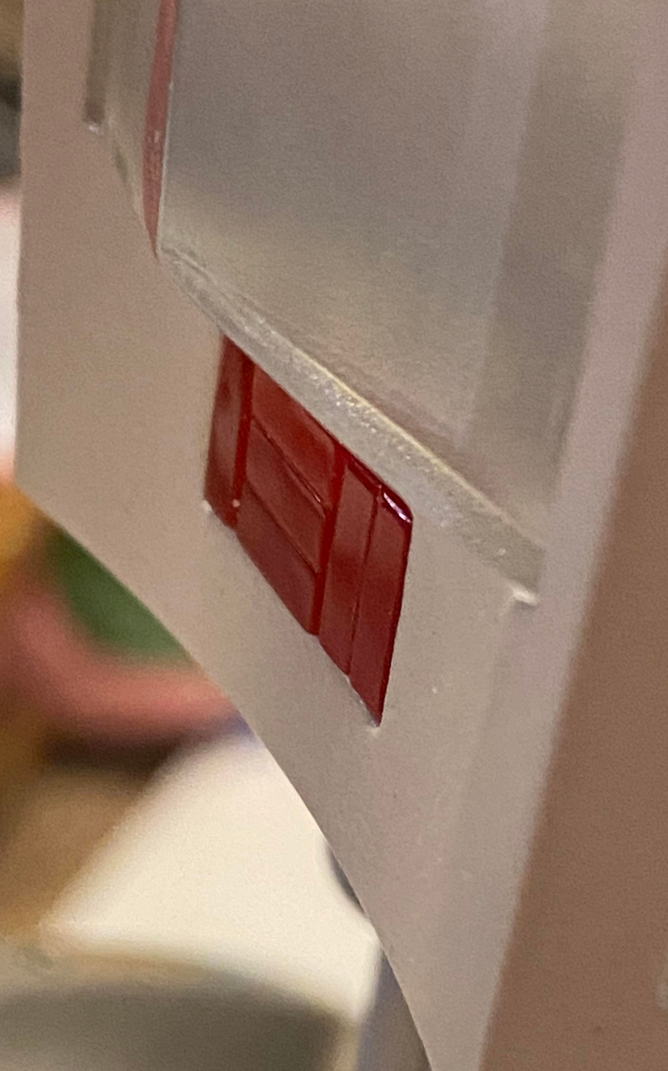
assets/338622038_1027298345303575_6589060000439139115_n.jpg
