drolsen/r2-periscope-lighting/assets/338732983_586520080075125_6736982428985907376_n.jpg

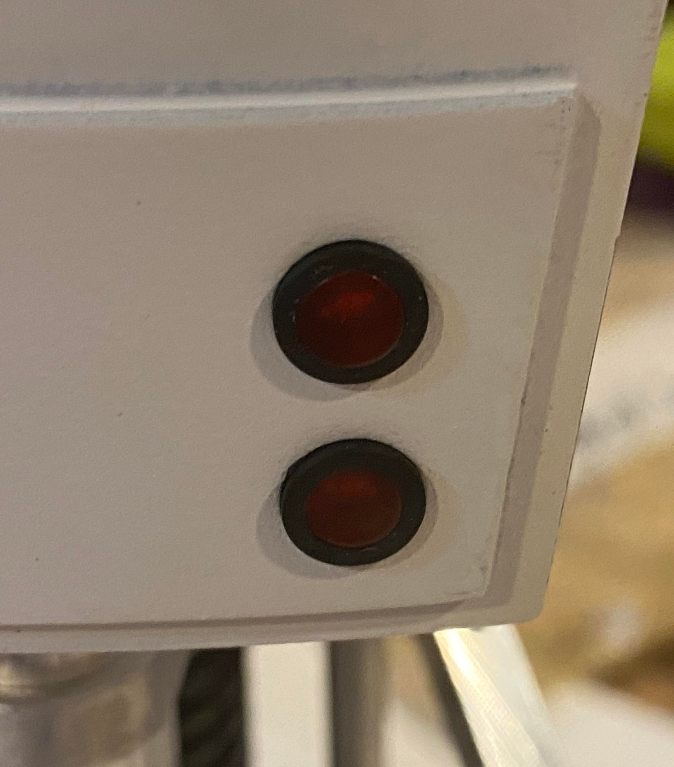
assets/338732983_586520080075125_6736982428985907376_n.jpg
