drolsen/r2-periscope-lighting/assets/fab-01.jpg

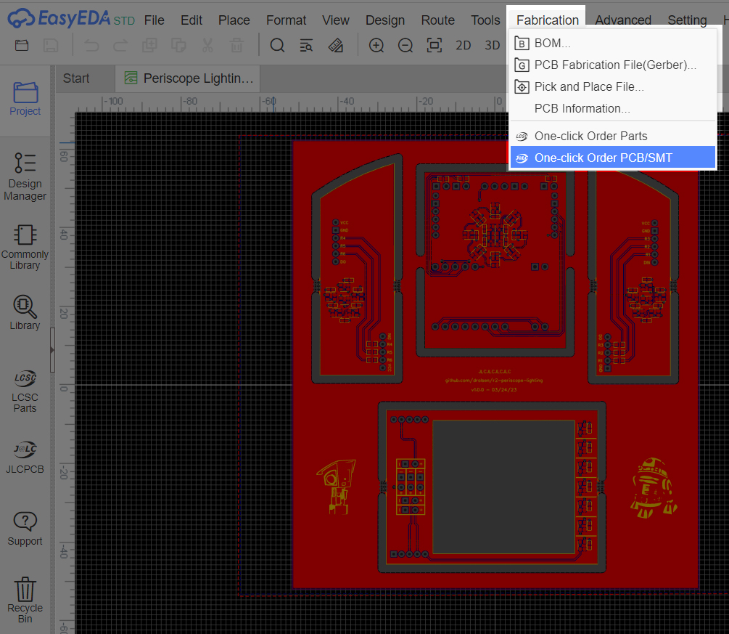
assets/fab-01.jpg
