drolsen/r2-periscope-lighting/assets/fab-01a.jpg

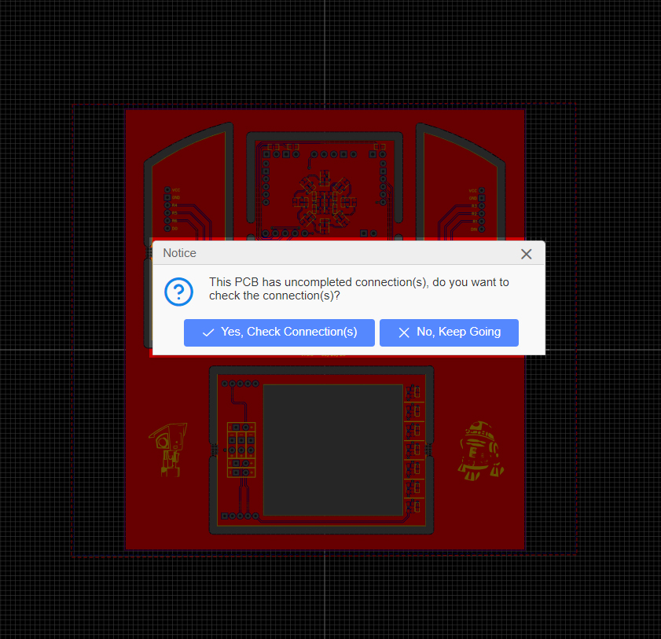
assets/fab-01a.jpg
