drolsen/r2-periscope-lighting/assets/fab-01b.jpg

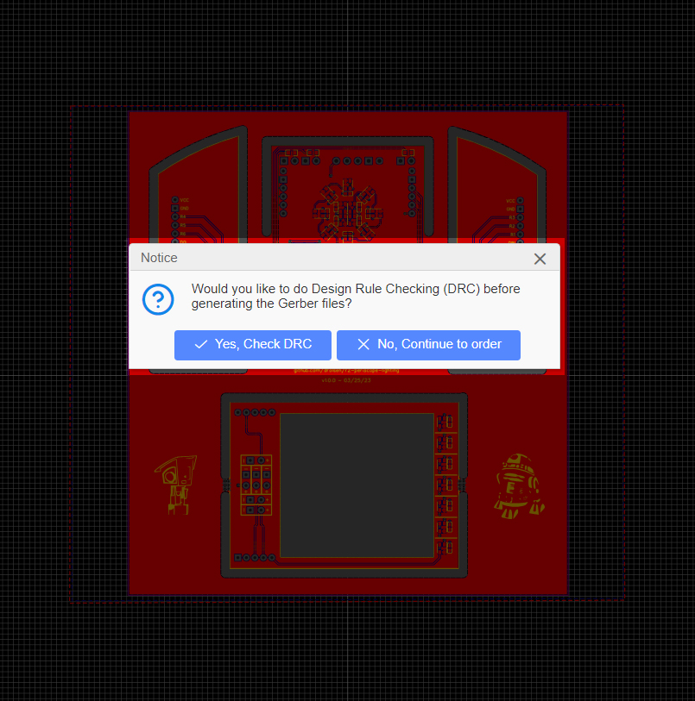
assets/fab-01b.jpg
