drolsen/r2-periscope-lighting/assets/fab-02.jpg

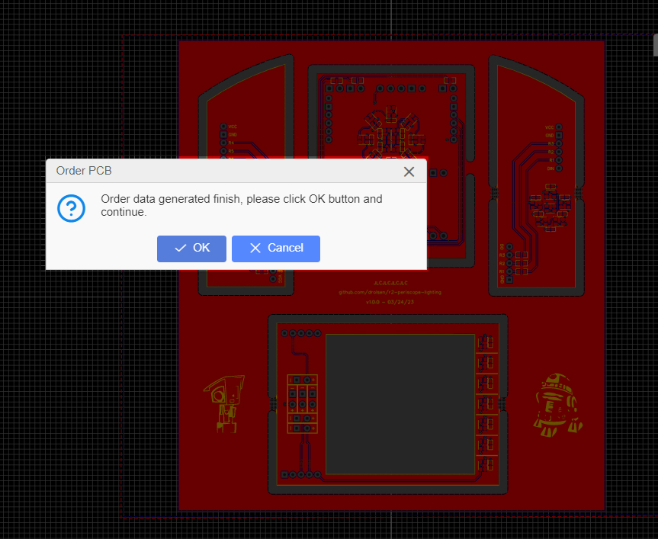
assets/fab-02.jpg
