drolsen/r2-periscope-lighting/assets/fab-03.jpg

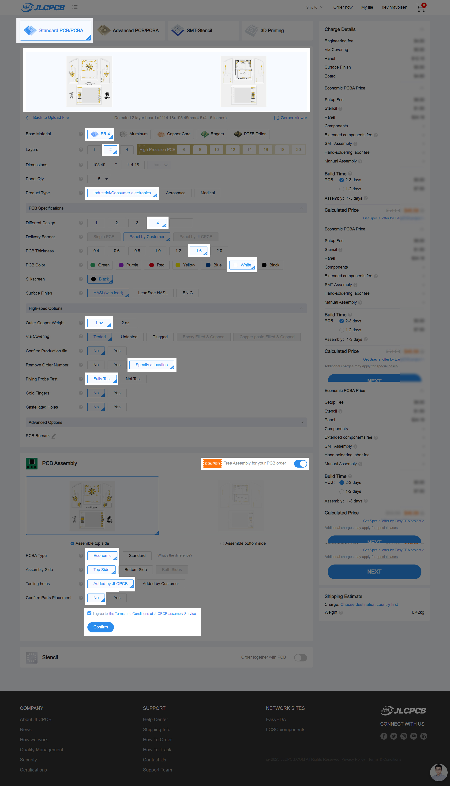
assets/fab-03.jpg
