drolsen/r2-periscope-lighting/assets/fab-03b.jpg

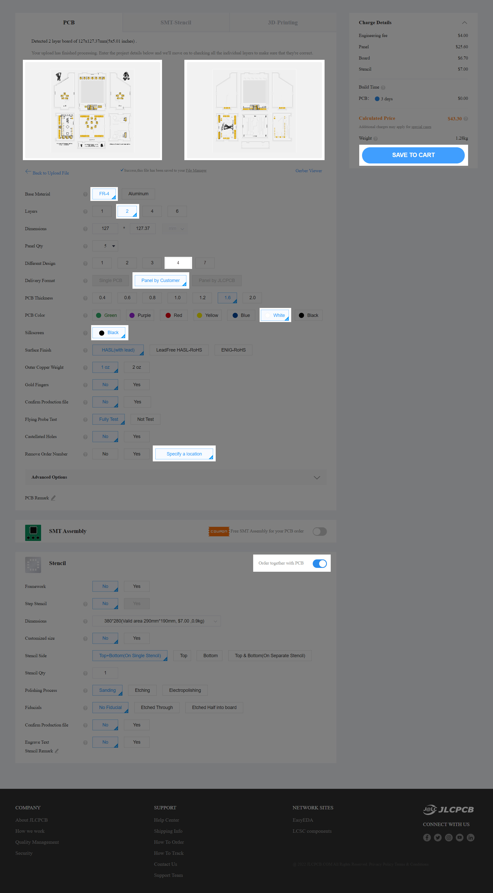
assets/fab-03b.jpg
