drolsen/r2-periscope-lighting/assets/fab-04.jpg

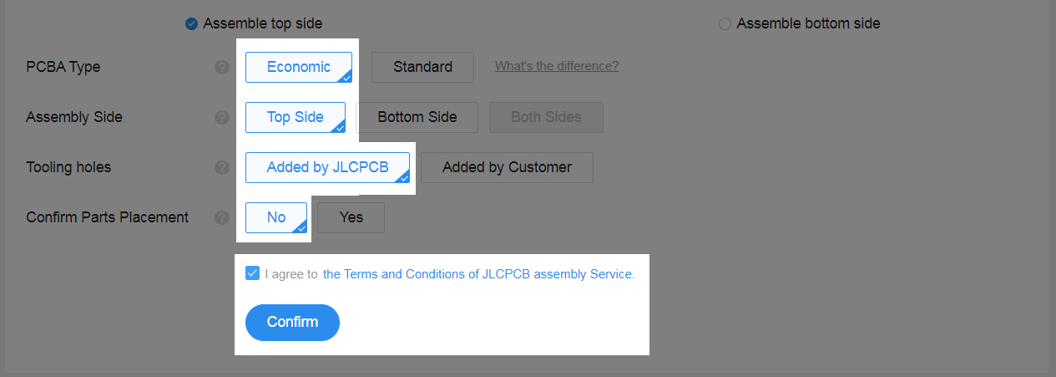
assets/fab-04.jpg
