drolsen/r2-periscope-lighting/assets/fab-05.jpg

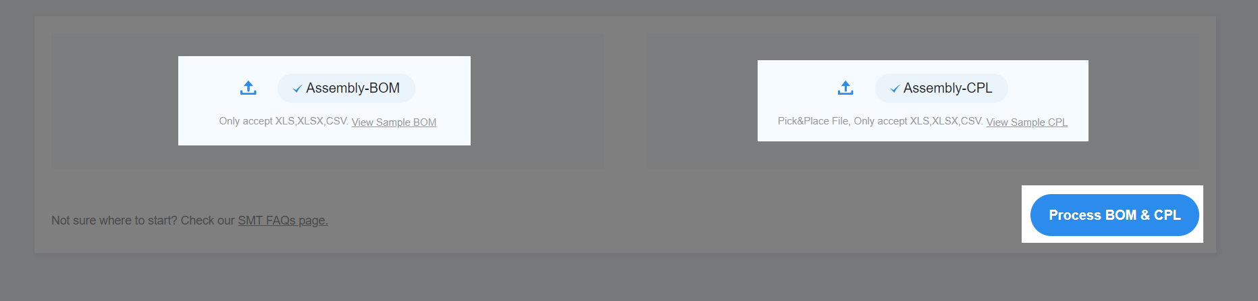
assets/fab-05.jpg
