drolsen/r2-periscope-lighting/assets/fab-06.jpg

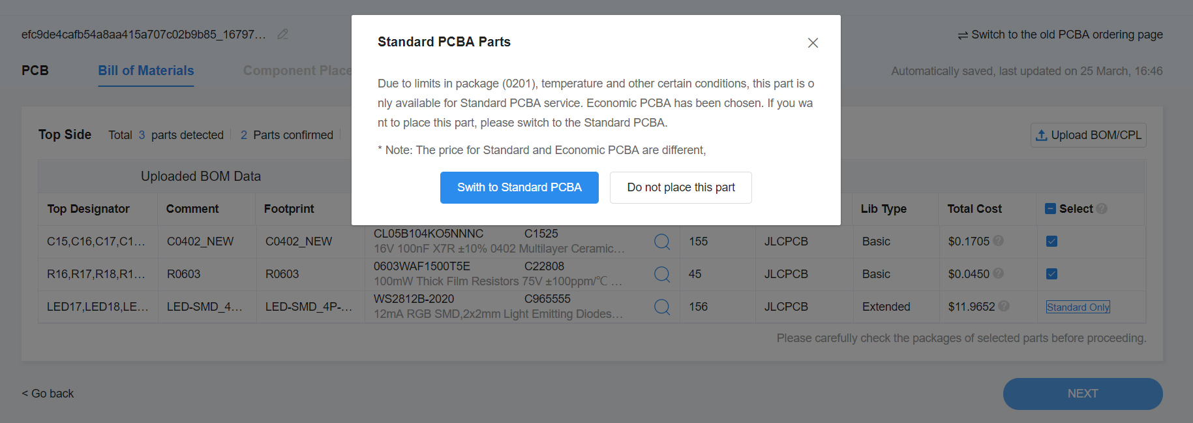
assets/fab-06.jpg
