drolsen/r2-periscope-lighting/assets/fab-06a.jpg

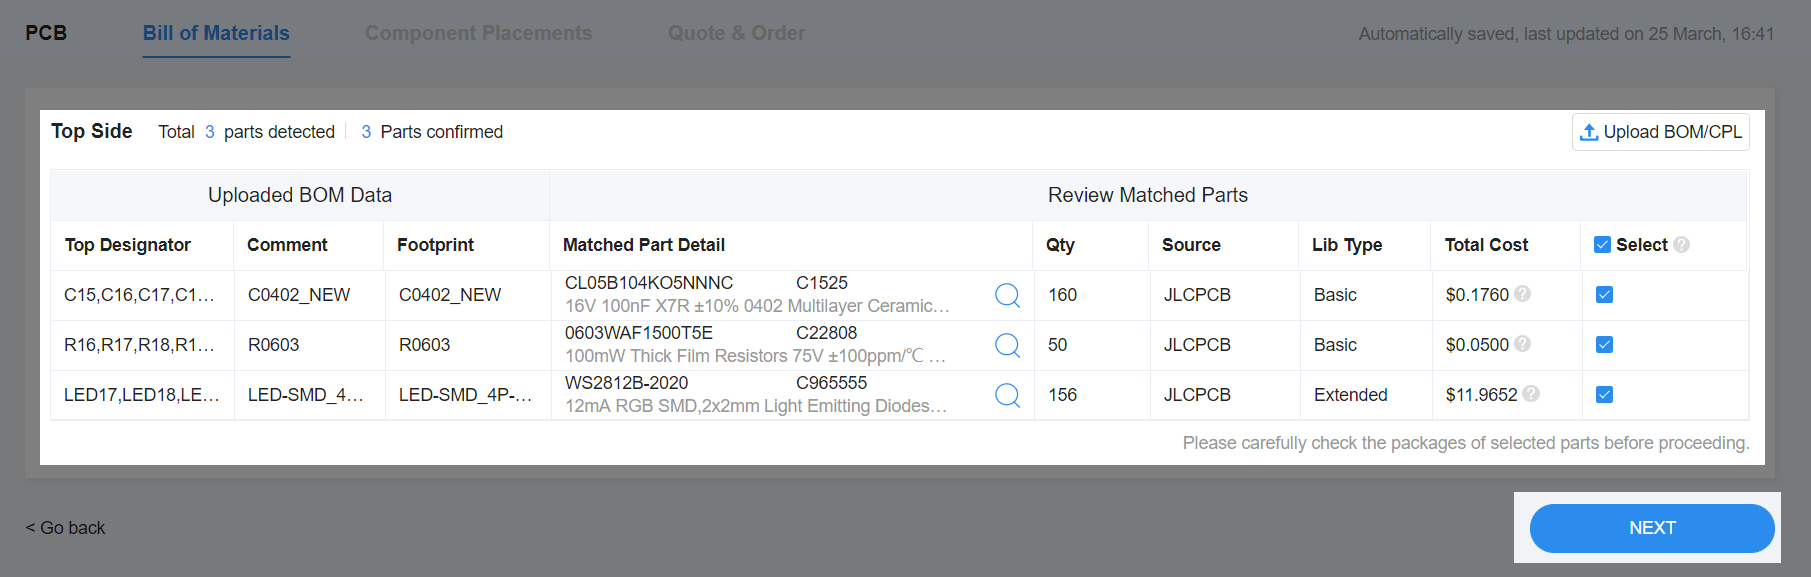
assets/fab-06a.jpg
