drolsen/r2-periscope-lighting/assets/fab-07.jpg

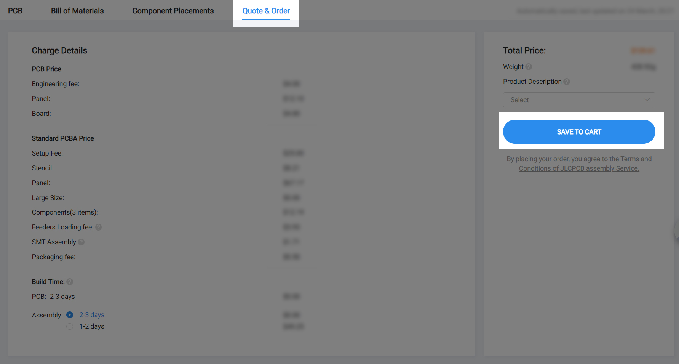
assets/fab-07.jpg
