drolsen/r2-periscope-lighting/models/Dome - STL/Tower & Combs/Tower Comb - Left10 Rev5.stl

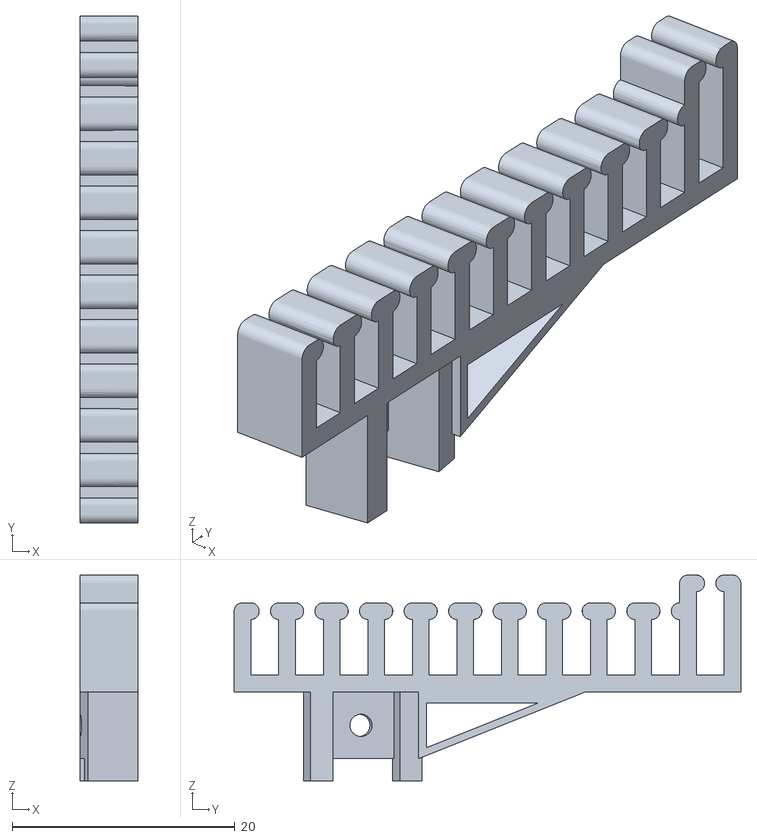
[picture p88: CAD file, 2023-03-23, last stored version]
models/Dome - STL/Tower & Combs/Tower Comb - Left10 Rev5.stl
5.25 x 45.5 x 18.5
