drolsen/r2-periscope-lighting/models/OBJ_Bottom.obj

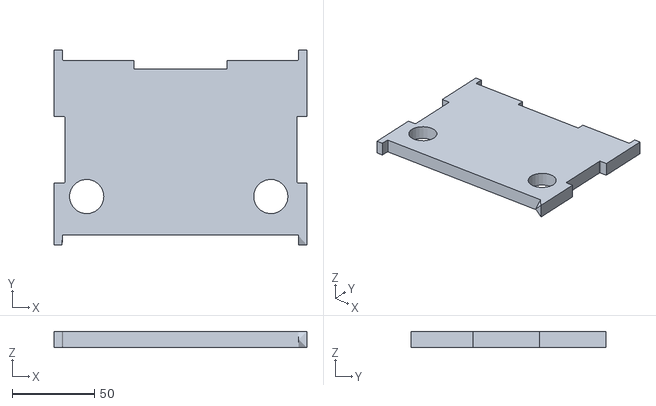
[picture p89: CAD file, 2023-03-23, last stored version]
models/OBJ_Bottom.obj
153.9 x 118.8 x 10.0
