drolsen/r2-periscope-lighting/models/Dome - STL/Combs/Comb 5x2 rev0.stl

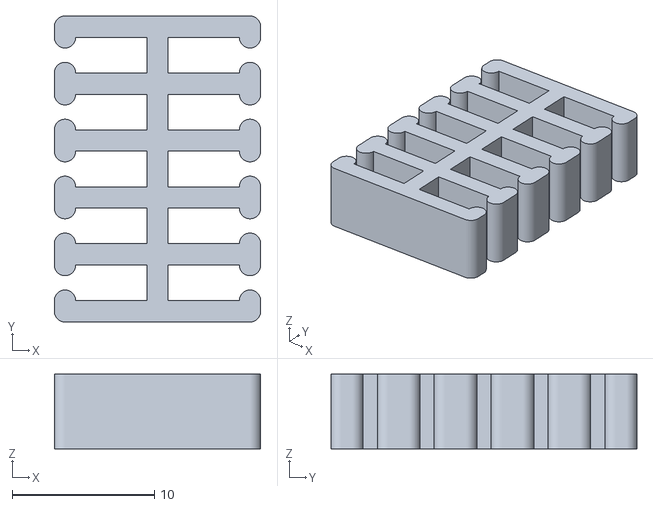
[picture p90: CAD file, 2023-03-23, last stored version]
models/Dome - STL/Combs/Comb 5x2 rev0.stl
14.5 x 21.5 x 5.25
