drolsen/r2-periscope-lighting/models/Dome - STL/Servo Clips/Servoclip original.stl

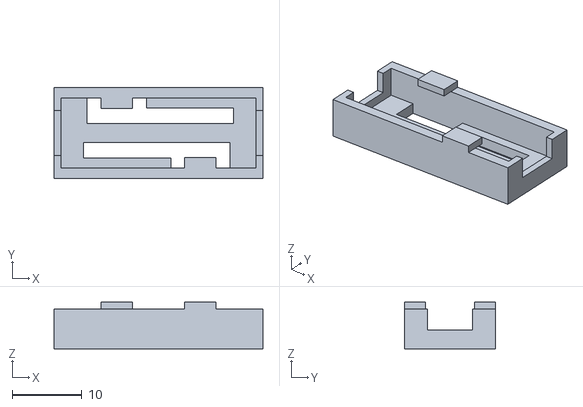
[picture p91: CAD file, 2023-03-23, last stored version]
models/Dome - STL/Servo Clips/Servoclip original.stl
30.0 x 13.0 x 6.70
