drolsen/r2-periscope-lighting/models/Dome - STL/Tower & Combs/Tower - Pie Panel Rev5.stl

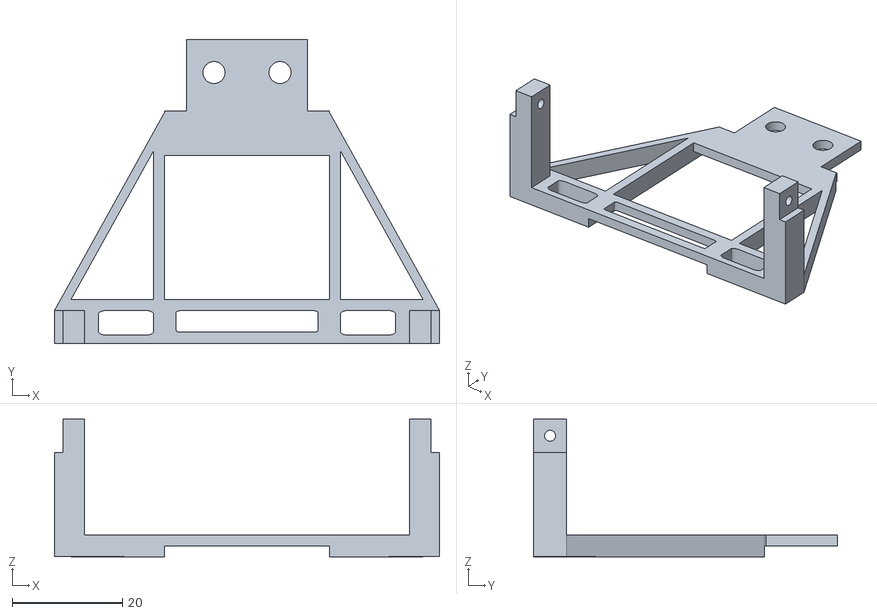
[picture p92: CAD file, 2023-03-23, last stored version]
models/Dome - STL/Tower & Combs/Tower - Pie Panel Rev5.stl
70.0 x 55.2 x 25.0
