drolsen/r2-periscope-lighting/models/OBJ_Back.obj

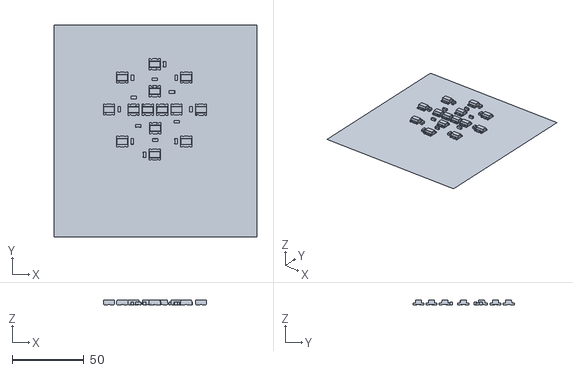
[picture p93: CAD file, 2023-03-23, last stored version]
models/OBJ_Back.obj
141.3 x 147.9 x 8.30
