drolsen/r2-periscope-lighting/models/Dome - STL/Servo Clips/Servoclip Mod1 - 2.stl

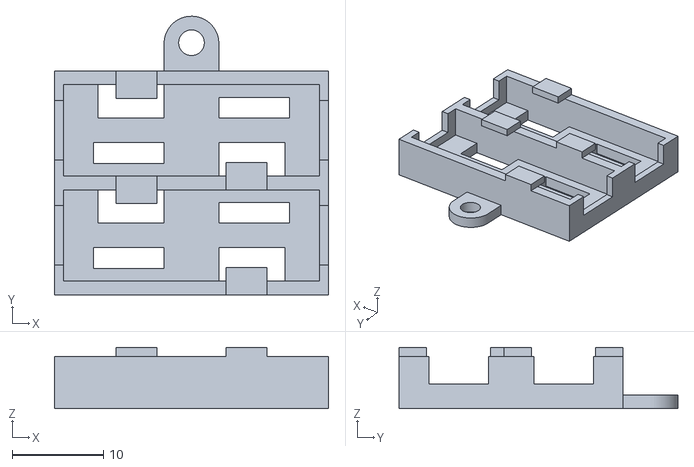
[picture p94: CAD file, 2023-03-23, last stored version]
models/Dome - STL/Servo Clips/Servoclip Mod1 - 2.stl
30.0 x 30.5 x 6.70
