drolsen/r2-periscope-lighting/models/Dome - STL/Tower & Combs/Tower - Empty Pie.stl

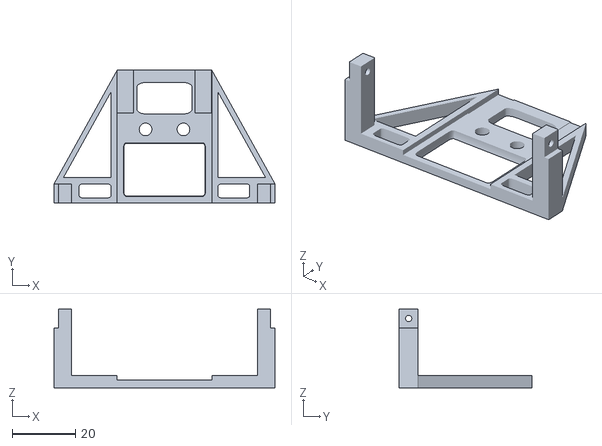
[picture p95: CAD file, 2023-03-23, last stored version]
models/Dome - STL/Tower & Combs/Tower - Empty Pie.stl
70.0 x 42.0 x 25.0
