drolsen/r2-periscope-lighting/models/Dome - STL/Tower & Combs/Tower Comb - Left11 Rev6.stl

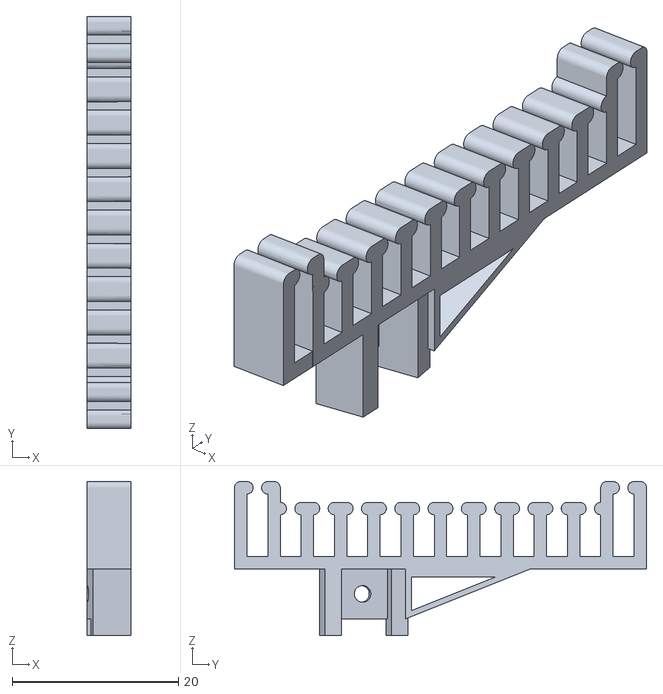
[picture p96: CAD file, 2023-03-23, last stored version]
models/Dome - STL/Tower & Combs/Tower Comb - Left11 Rev6.stl
5.25 x 49.5 x 18.5
