drolsen/r2-periscope-lighting/models/Dome - STL/Tower & Combs/Tower - Panel 13 Rev3.stl

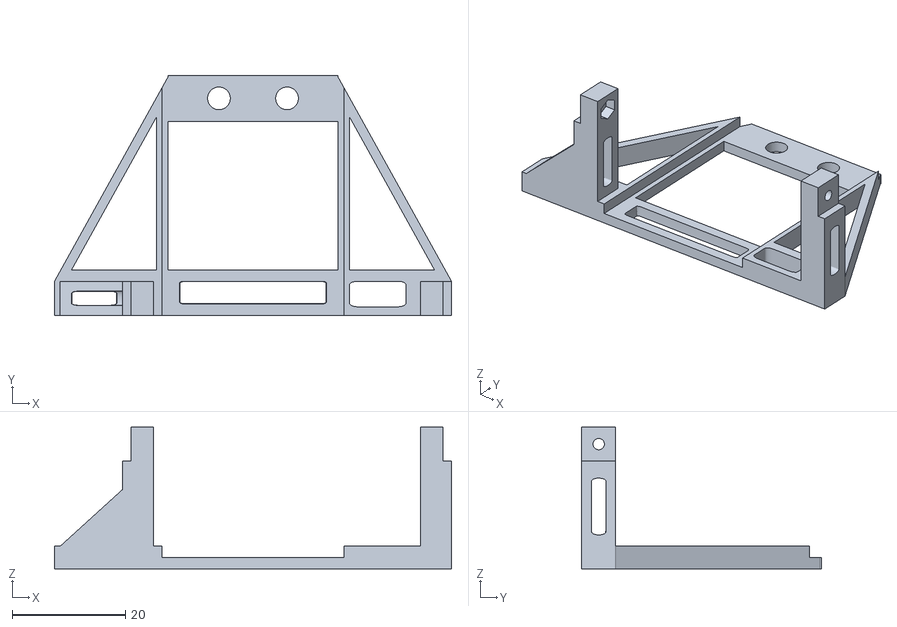
[picture p97: CAD file, 2023-03-23, last stored version]
models/Dome - STL/Tower & Combs/Tower - Panel 13 Rev3.stl
70.0 x 42.2 x 25.0
